cruzryan/OpenDOG/CAD/STL/b2/InterConnector.STL

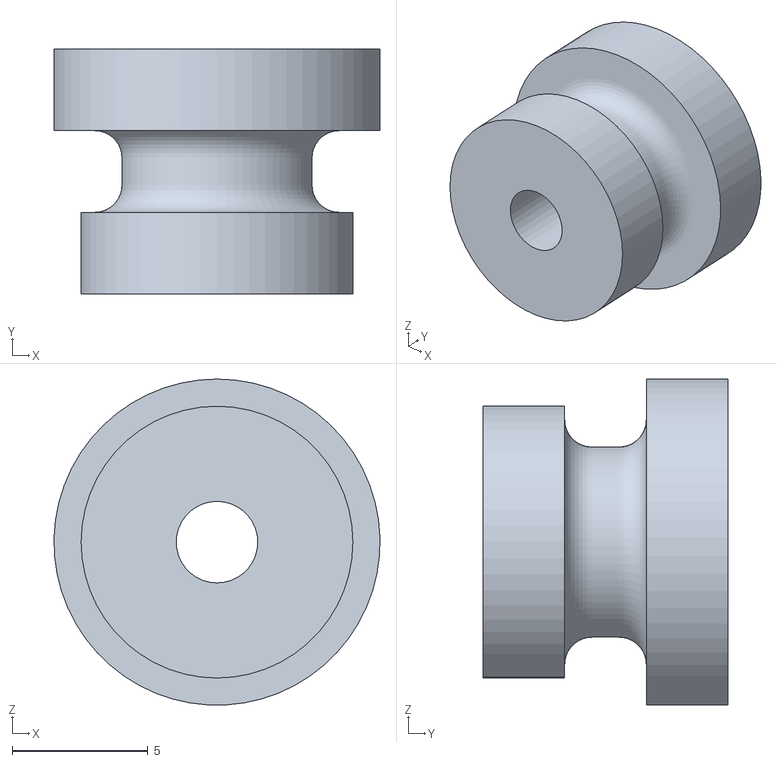
[picture p18: CAD file, 2025-06-15]
CAD/STL/b2/InterConnector.STL
12.0 x 9.00 x 12.0
