cruzryan/OpenDOG/CAD/STL/FINAL/A.STL

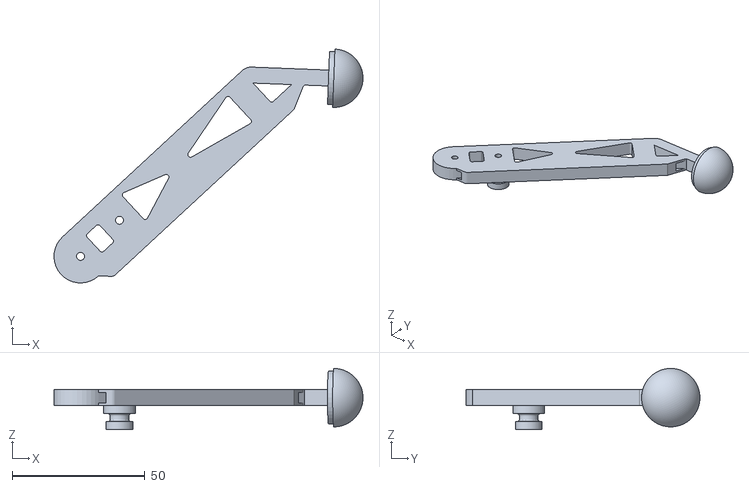
[picture p19: CAD file, 2025-06-15]
CAD/STL/FINAL/A.STL
116.4 x 88.0 x 23.0
