cruzryan/OpenDOG/CAD/STL/FULL/Chasis.STL

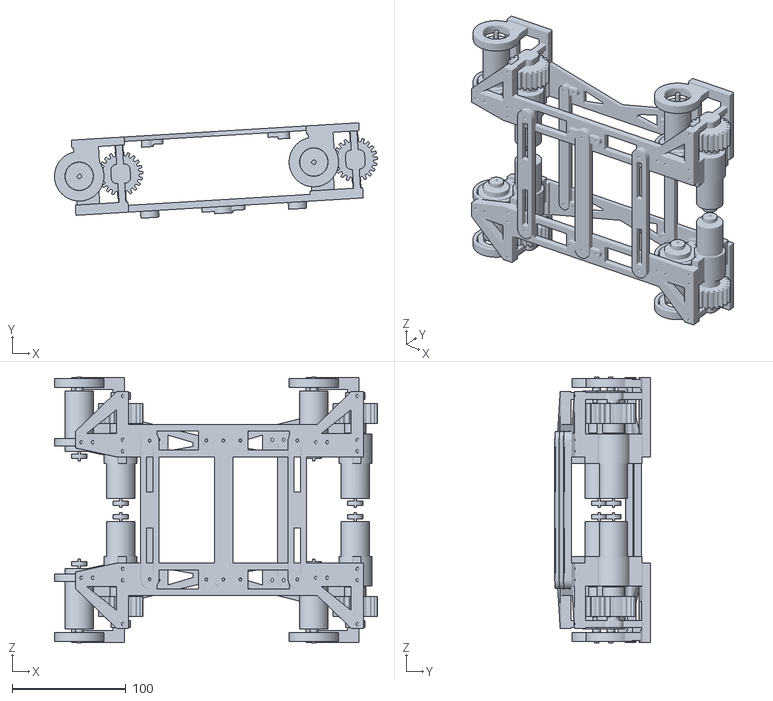
[picture p20: CAD file, 2025-06-15]
CAD/STL/FULL/Chasis.STL
283.8 x 83.9 x 233.7
