cruzryan/OpenDOG/CAD/STL/LEG/ShittyLeg - Cople-1.STL

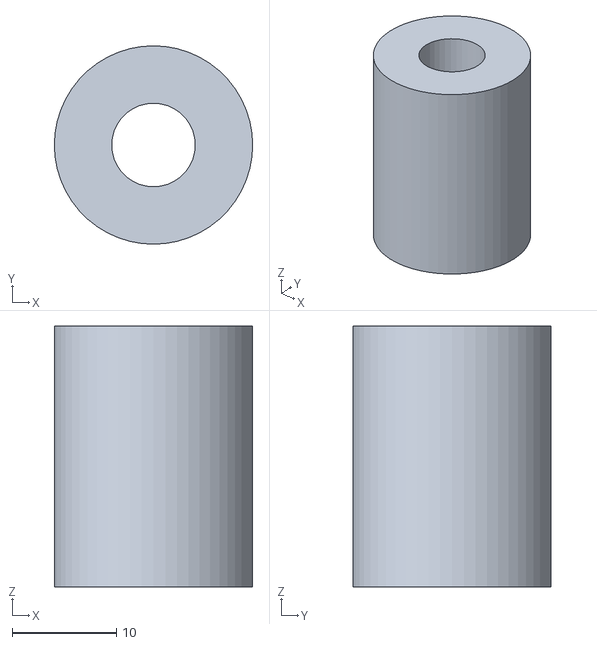
[picture p21: CAD file, 2025-06-15]
CAD/STL/LEG/ShittyLeg - Cople-1.STL
19.0 x 19.0 x 25.0
