cruzryan/OpenDOG/Code/mujoco/unitree_go1/assets/hip.stl

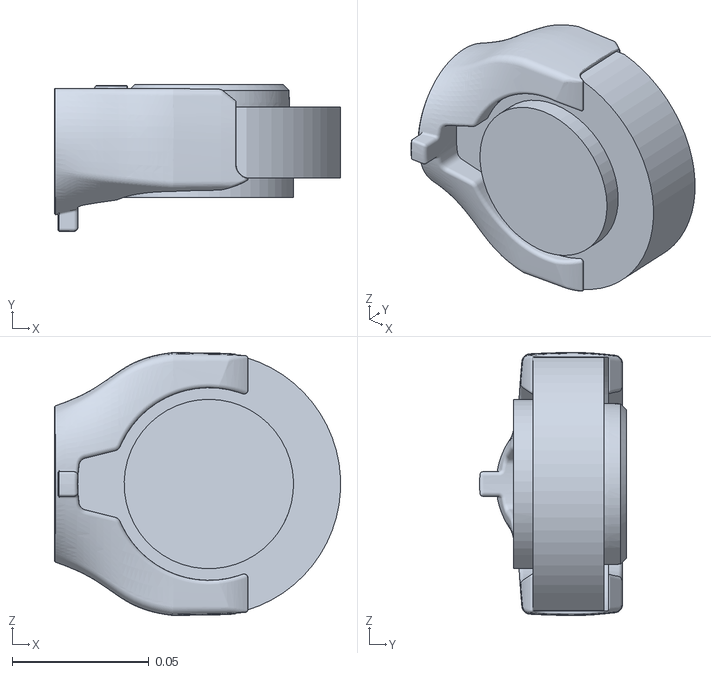
[picture p22: CAD file, 2025-03-04]
Code/mujoco/unitree_go1/assets/hip.stl
0.105 x 0.0538 x 0.0963
