cruzryan/OpenDOG/CAD/STL/b1/FeetLigament.STL

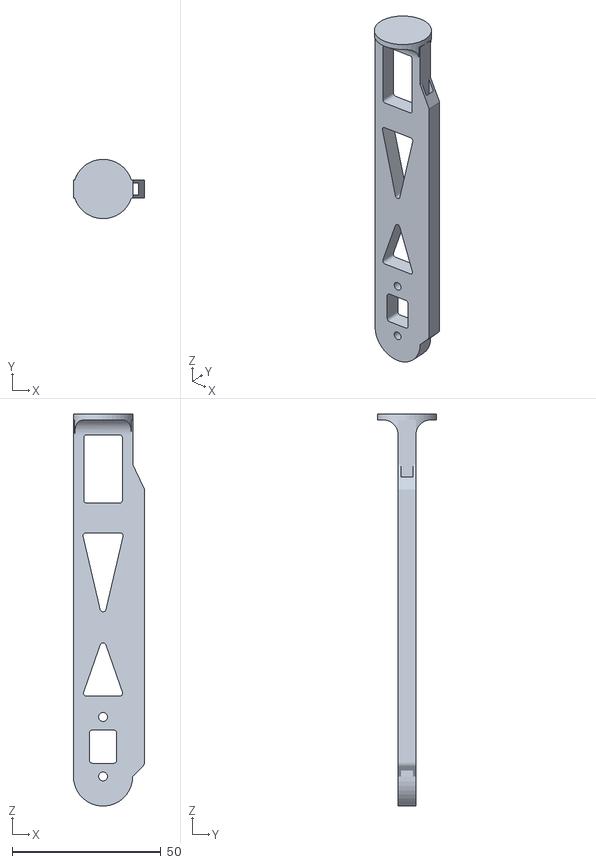
[picture p23: CAD file, 2025-06-15]
CAD/STL/b1/FeetLigament.STL
24.0 x 20.0 x 132.0
