cruzryan/OpenDOG/CAD/STL/b3/Balero6mmHolder.STL

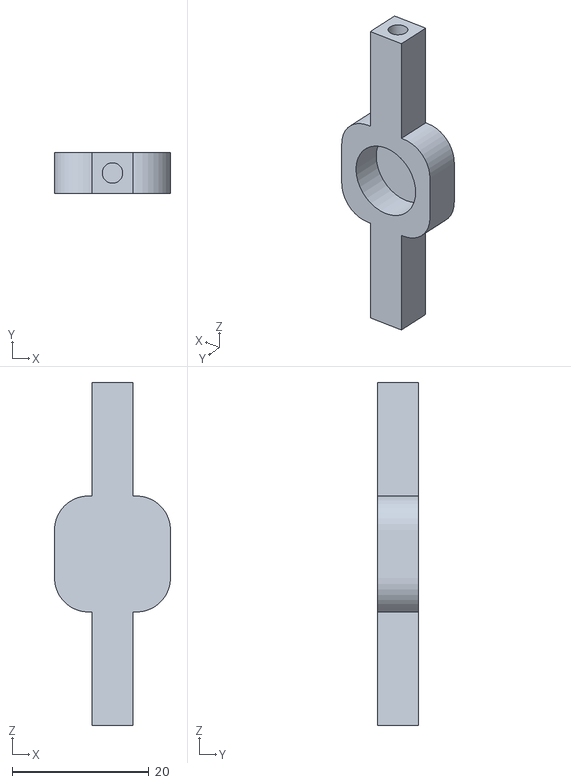
[picture p24: CAD file, 2025-06-15]
CAD/STL/b3/Balero6mmHolder.STL
17.0 x 6.00 x 50.2
