cruzryan/OpenDOG/CAD/STL/LEG/ShittyLeg - MotorCopler-1.STL

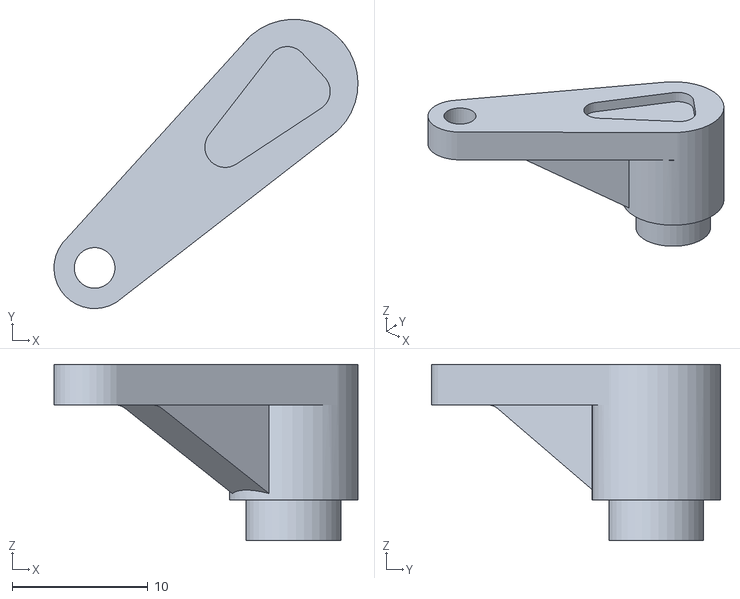
[picture p25: CAD file, 2025-06-15]
CAD/STL/LEG/ShittyLeg - MotorCopler-1.STL
22.4 x 21.3 x 13.0
