cruzryan/OpenDOG/CAD/STL/MUJOCO/ShittyLeg.STL

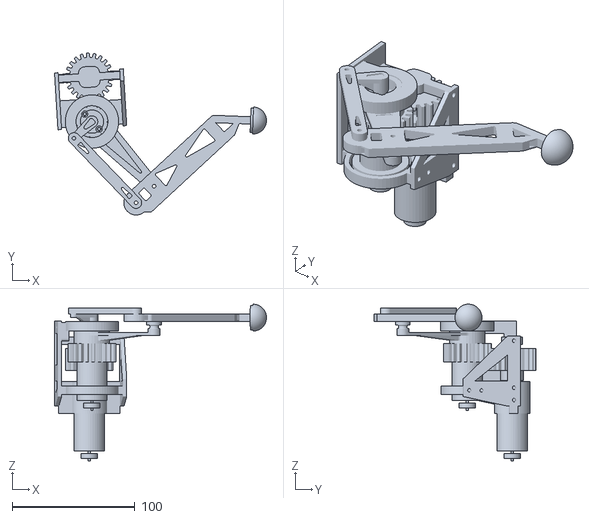
[picture p26: CAD file, 2025-06-15]
CAD/STL/MUJOCO/ShittyLeg.STL
172.9 x 132.1 x 127.8
