cruzryan/OpenDOG/CAD/STL/TopLegConnectorFIXEDLOL.STL

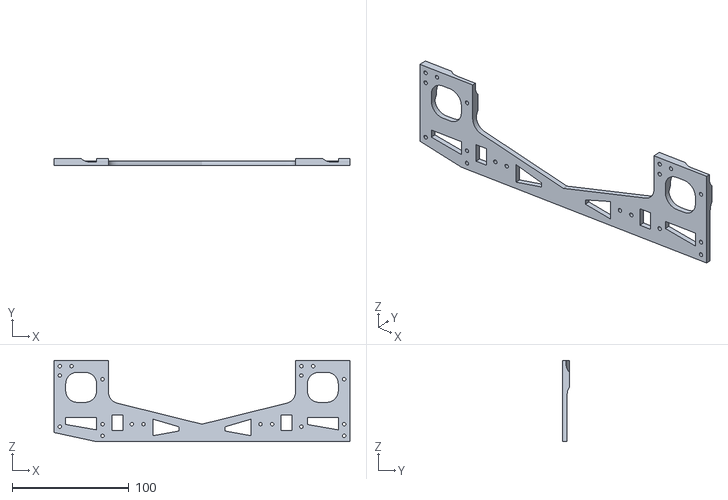
[picture p27: CAD file, 2025-06-15]
CAD/STL/TopLegConnectorFIXEDLOL.STL
253.0 x 6.00 x 69.6
