cruzryan/OpenDOG/Code/mujoco/our_robot/assets/left_calf.stl

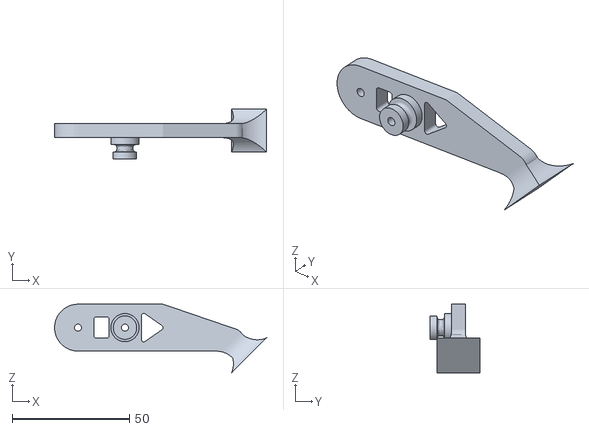
[picture p28: CAD file, 2025-05-04]
Code/mujoco/our_robot/assets/left_calf.stl
90.2 x 21.1 x 29.3
