cruzryan/OpenDOG/Code/mujoco/unitree_go1/assets/calf.stl

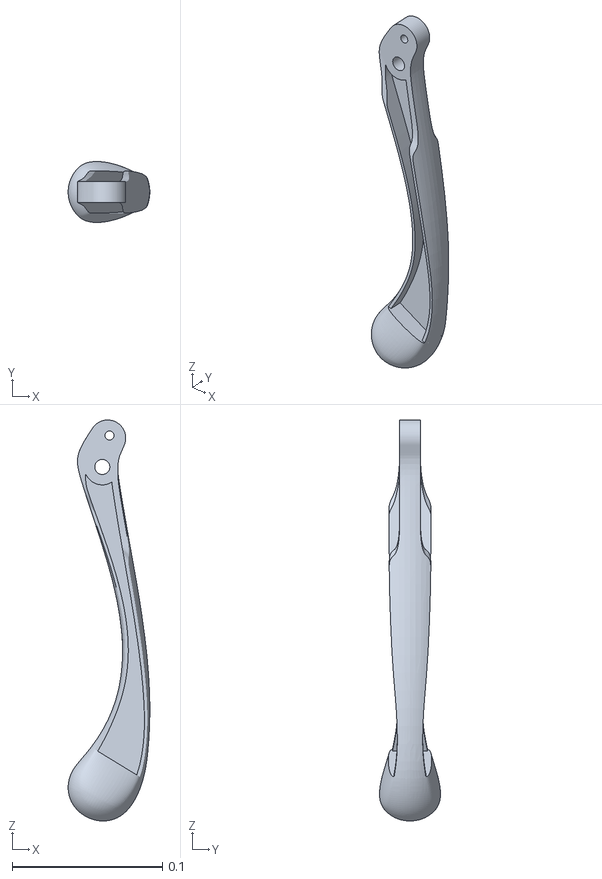
[picture p29: CAD file, 2025-03-04]
Code/mujoco/unitree_go1/assets/calf.stl
0.0543 x 0.0405 x 0.266
