cruzryan/OpenDOG/CAD/STL/b3/FeetLigament.STL

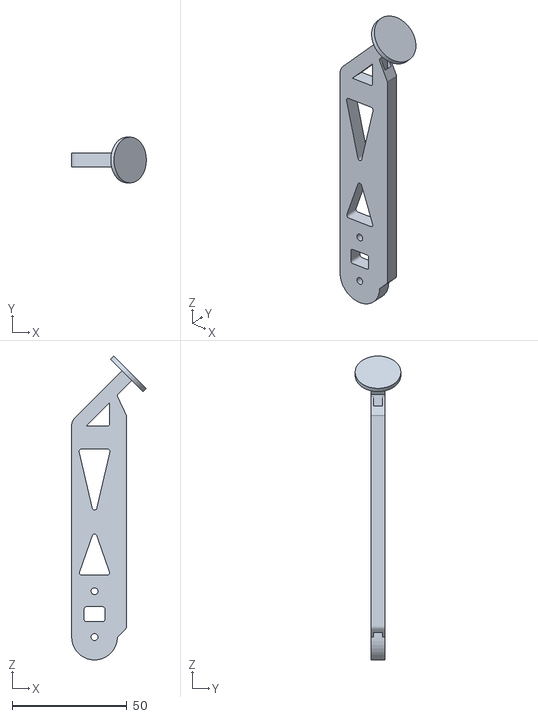
[picture p30: CAD file, 2025-06-15]
CAD/STL/b3/FeetLigament.STL
32.6 x 20.0 x 132.6
