cruzryan/OpenDOG/CAD/STL/TopLegConnector FILLED.STL

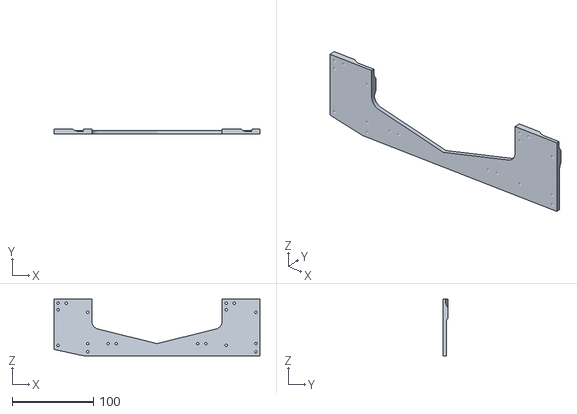
[picture p31: CAD file, 2025-06-15]
CAD/STL/TopLegConnector FILLED.STL
253.0 x 6.00 x 69.6
