cruzryan/OpenDOG/Code/mujoco/our_robot/assets/chasis.stl

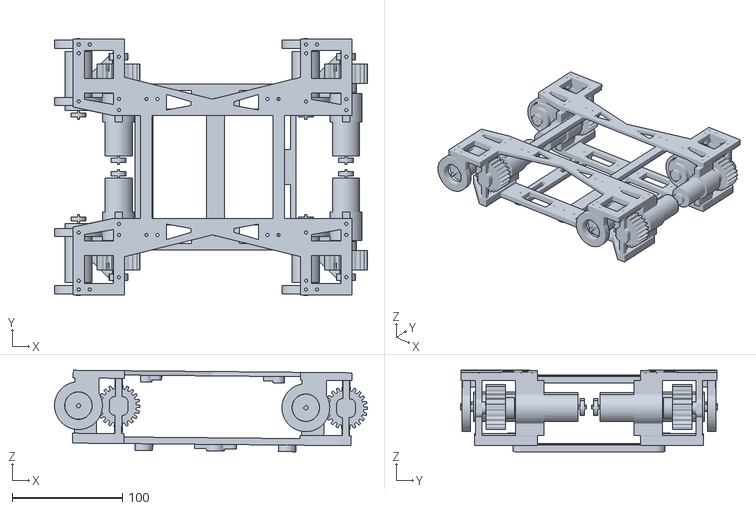
[picture p32: CAD file, 2025-05-04]
Code/mujoco/our_robot/assets/chasis.stl
284.3 x 233.7 x 74.1
