cruzryan/OpenDOG/Code/mujoco/unitree_go1/assets/thigh_mirror.stl

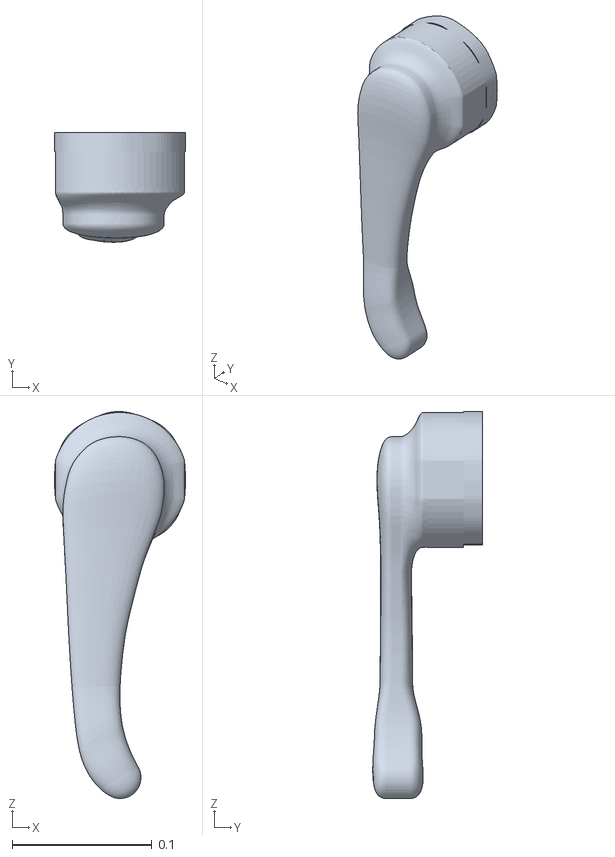
[picture p33: CAD file, 2025-03-04]
Code/mujoco/unitree_go1/assets/thigh_mirror.stl
0.094 x 0.0784 x 0.277
