cruzryan/OpenDOG/CAD/STL/b1/PartConnector.STL

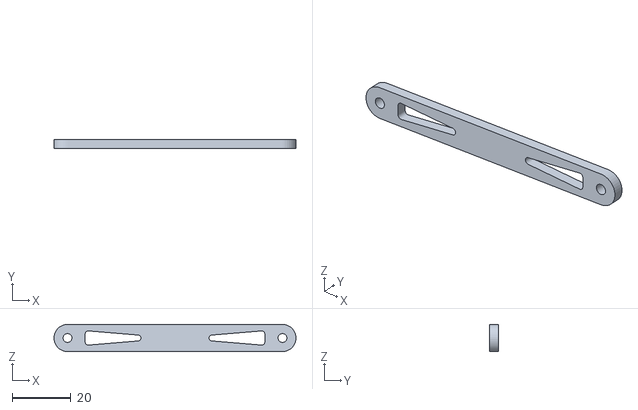
[picture p34: CAD file, 2025-06-15]
CAD/STL/b1/PartConnector.STL
82.2 x 3.00 x 9.22
