cruzryan/OpenDOG/CAD/STL/b3/TopConnectorLeg.STL

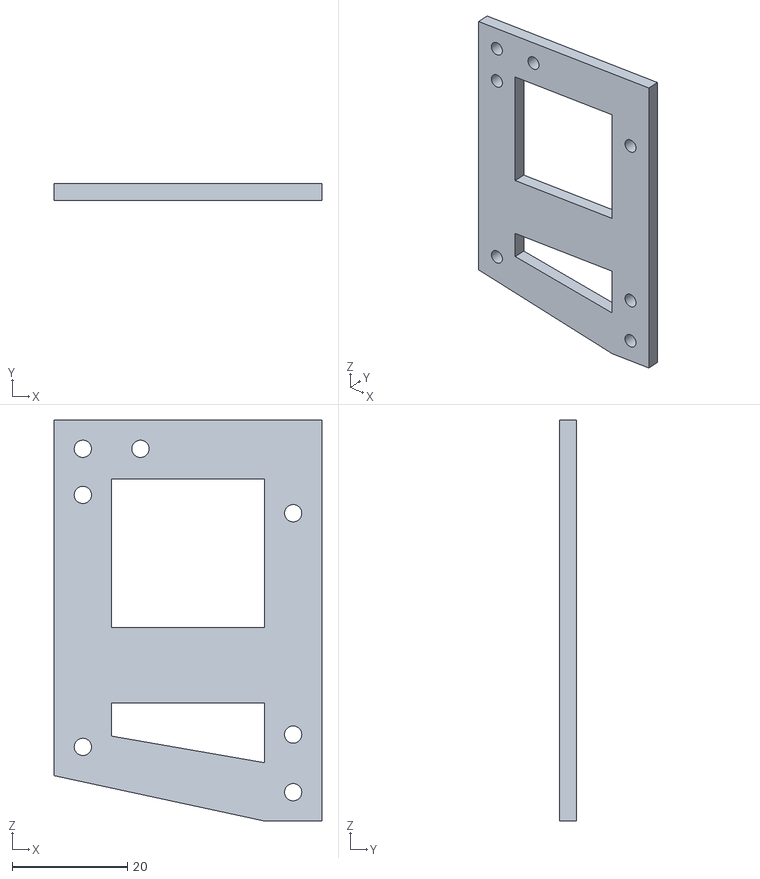
[picture p35: CAD file, 2025-06-15]
CAD/STL/b3/TopConnectorLeg.STL
46.5 x 3.00 x 69.6
