cruzryan/OpenDOG/CAD/STL/BALERO A.STL

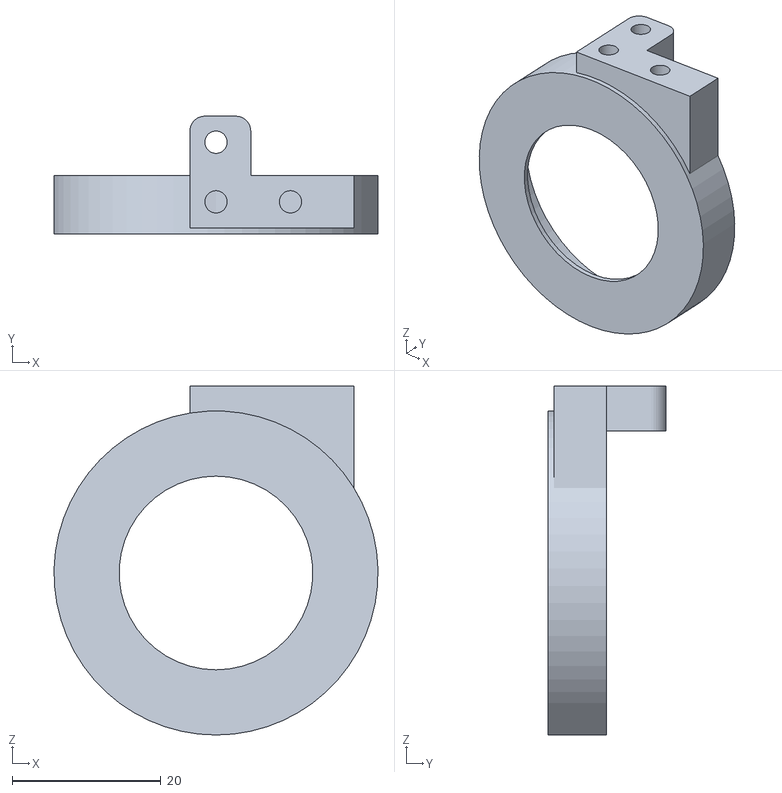
[picture p36: CAD file, 2025-06-15]
CAD/STL/BALERO A.STL
43.5 x 15.8 x 46.8
