cruzryan/OpenDOG/CAD/STL/FINAL/ENGRANE.STL

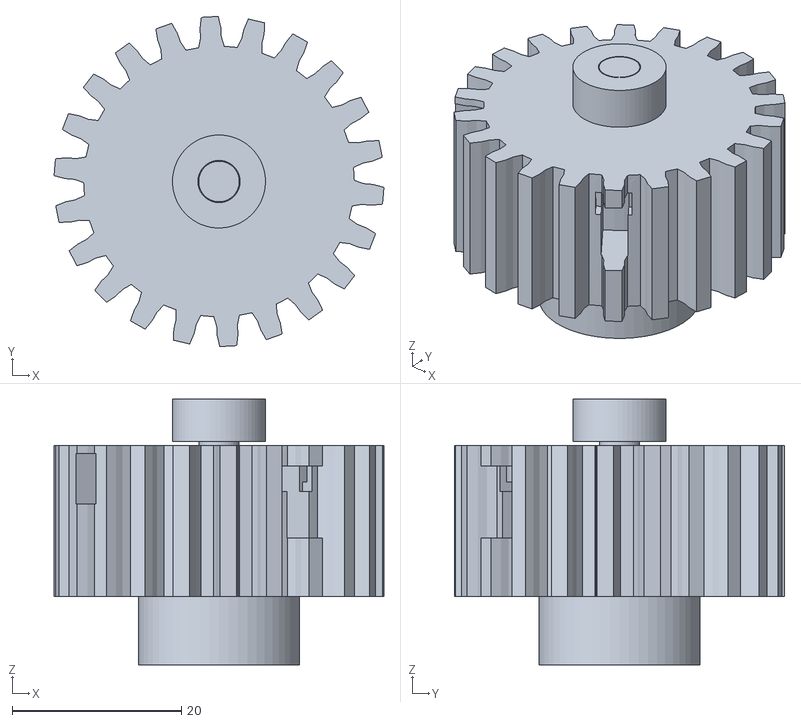
[picture p37: CAD file, 2025-06-15]
CAD/STL/FINAL/ENGRANE.STL
39.0 x 39.1 x 31.4
