cruzryan/OpenDOG/CAD/STL/LEG/ShittyLeg - PartConnector-1.STL

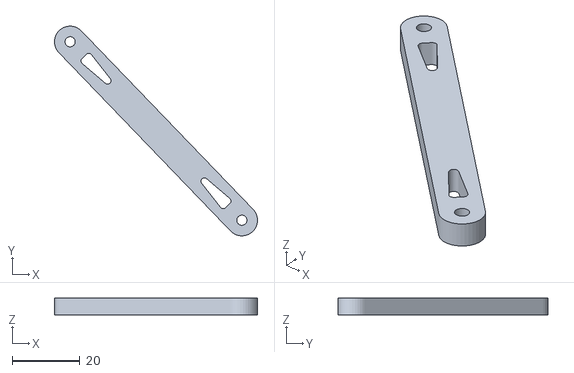
[picture p38: CAD file, 2025-06-15]
CAD/STL/LEG/ShittyLeg - PartConnector-1.STL
59.8 x 61.8 x 5.00
