cruzryan/OpenDOG/CAD/STL/MUJOCO/B.STL

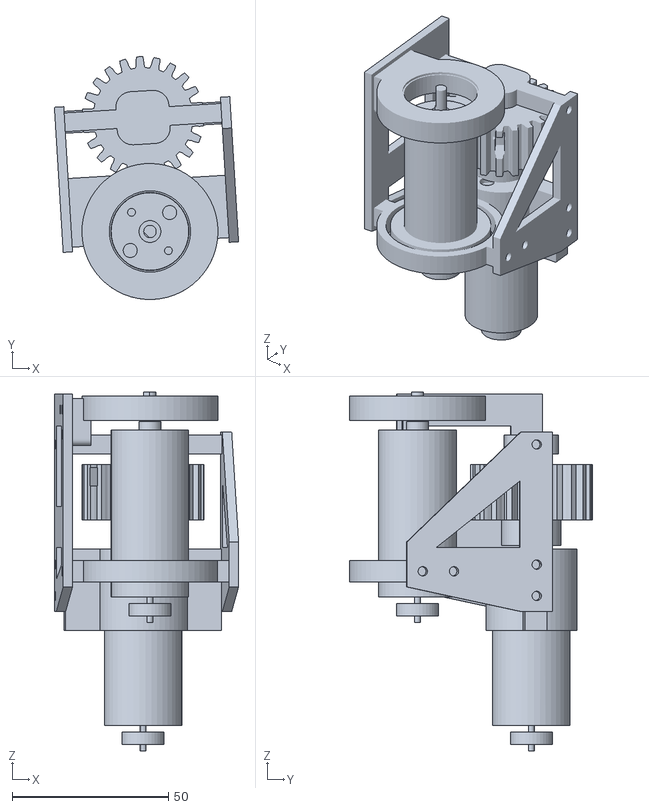
[picture p39: CAD file, 2025-06-15]
CAD/STL/MUJOCO/B.STL
58.9 x 77.7 x 114.8
