cruzryan/OpenDOG/CAD/STL/LEG/ShittyLeg - Balero-1.STL

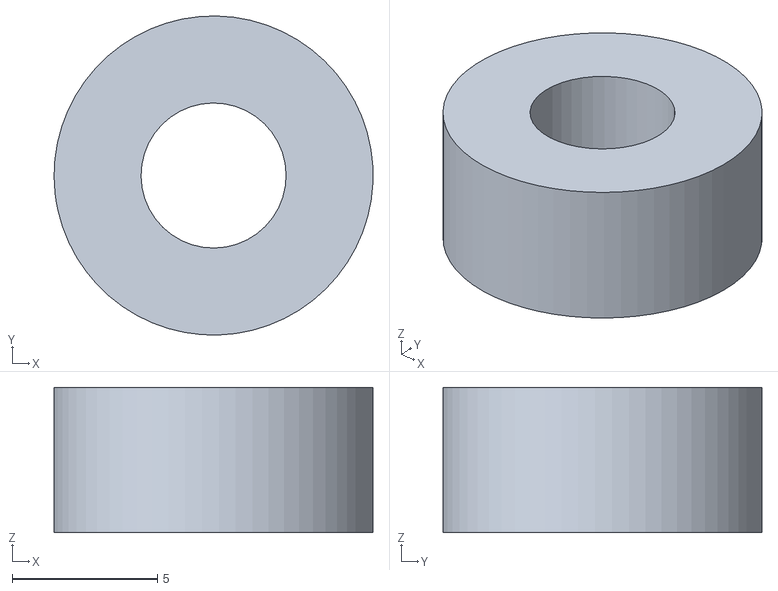
[picture p40: CAD file, 2025-06-15]
CAD/STL/LEG/ShittyLeg - Balero-1.STL
11.0 x 11.0 x 5.00
