cruzryan/OpenDOG/Code/mujoco/our_robot/assets/paw.stl

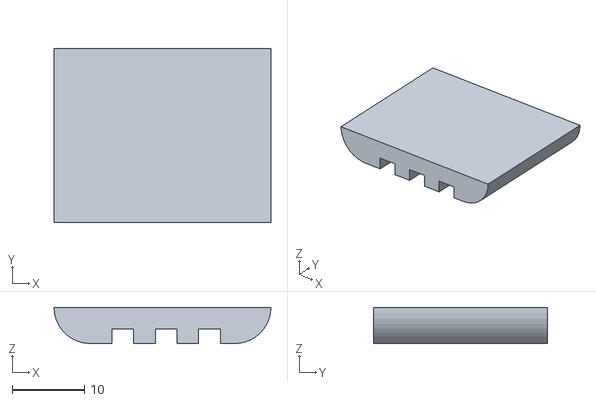
[picture p41: CAD file, 2025-05-04]
Code/mujoco/our_robot/assets/paw.stl
30.0 x 24.0 x 4.98
