cruzryan/OpenDOG/CAD/STL/ft.STL

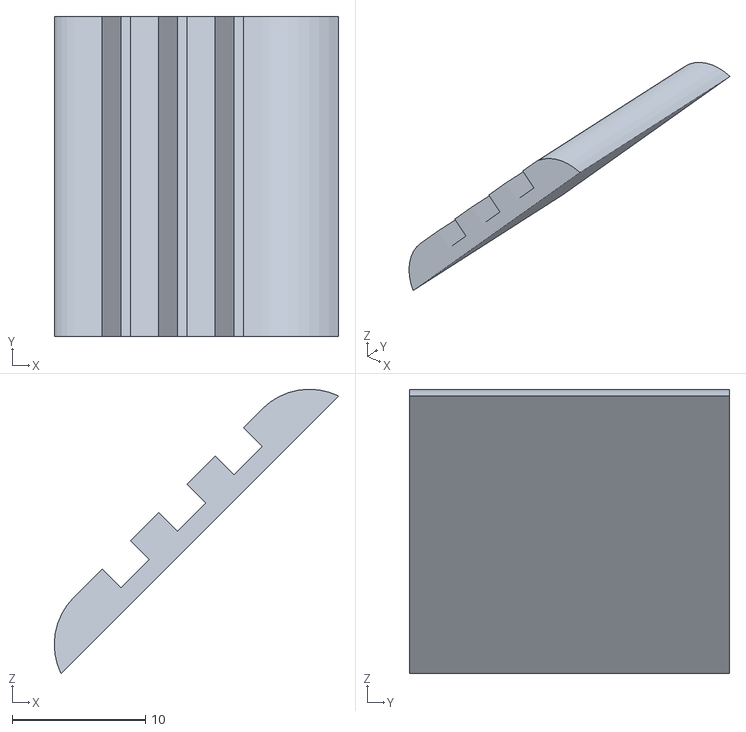
[picture p42: CAD file, 2025-06-15]
CAD/STL/ft.STL
21.3 x 24.0 x 21.3
