cruzryan/OpenDOG/CAD/STL/LEG/ShittyLeg - Motor GM25 V1-1.STL

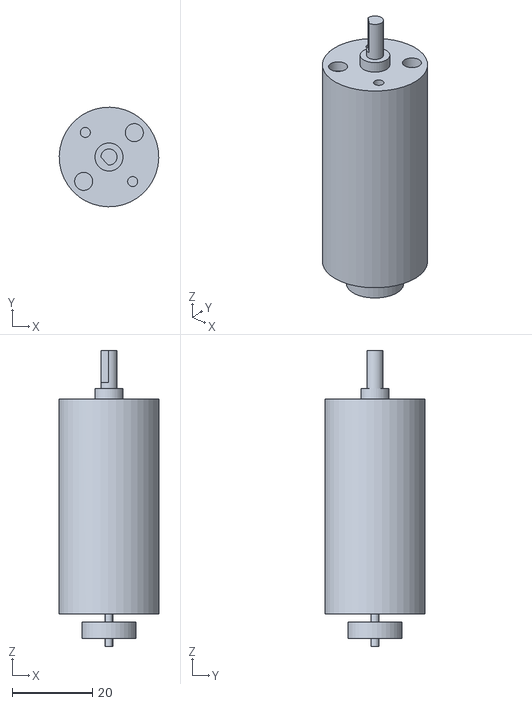
[picture p43: CAD file, 2025-06-15]
CAD/STL/LEG/ShittyLeg - Motor GM25 V1-1.STL
24.8 x 24.8 x 73.7
