cruzryan/OpenDOG/CAD/STL/b3/MotorCover2.STL

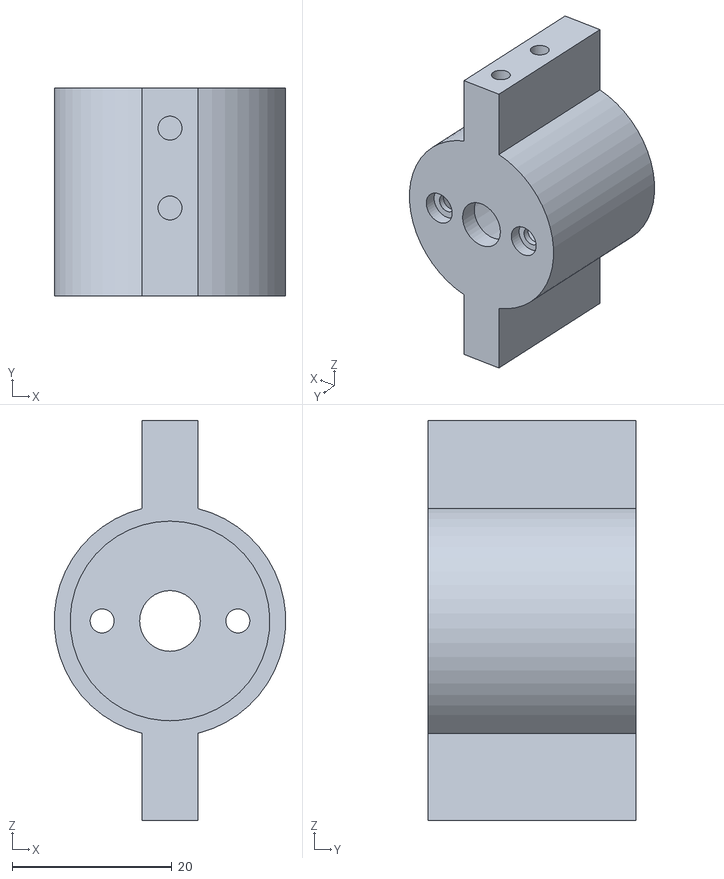
[picture p44: CAD file, 2025-06-15]
CAD/STL/b3/MotorCover2.STL
28.9 x 26.0 x 50.1
