cruzryan/OpenDOG/CAD/STL/CHASIS_NO_TRIG.stl

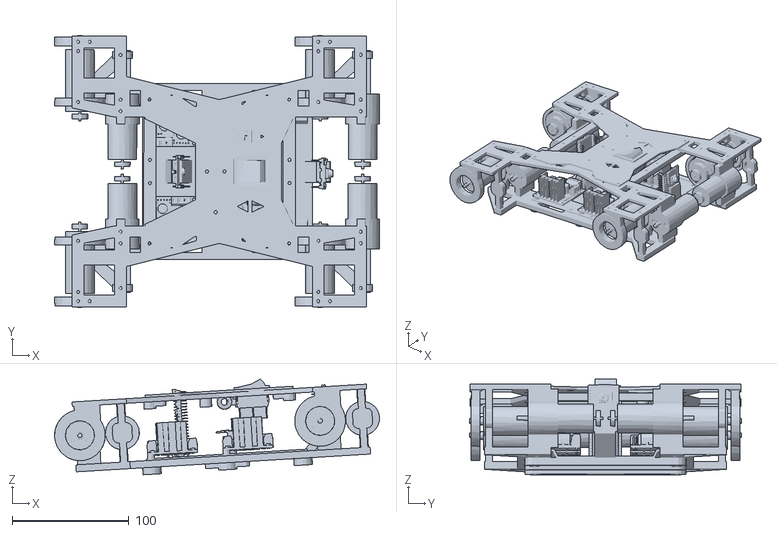
[picture p45: CAD file, 2025-06-15]
CAD/STL/CHASIS_NO_TRIG.stl
278.9 x 233.8 x 82.1
