cruzryan/OpenDOG/CAD/STL/LEG/ShittyLeg - Balero25mmv5-1.STL

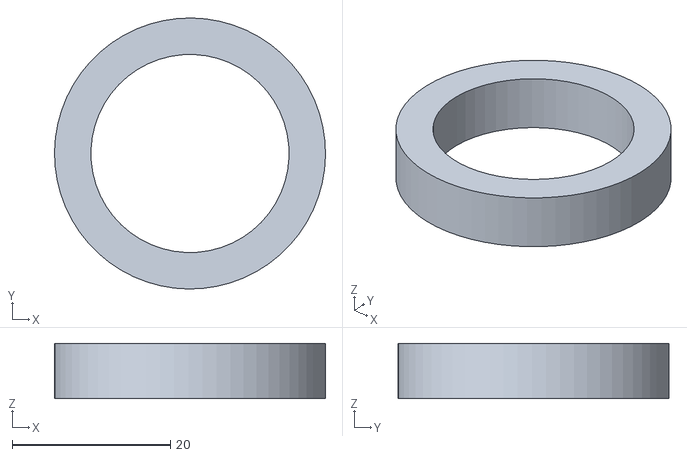
[picture p46: CAD file, 2025-06-15]
CAD/STL/LEG/ShittyLeg - Balero25mmv5-1.STL
34.2 x 34.2 x 7.00
