cruzryan/OpenDOG/CAD/STL/b3/BottomConnectorLeg3.STL

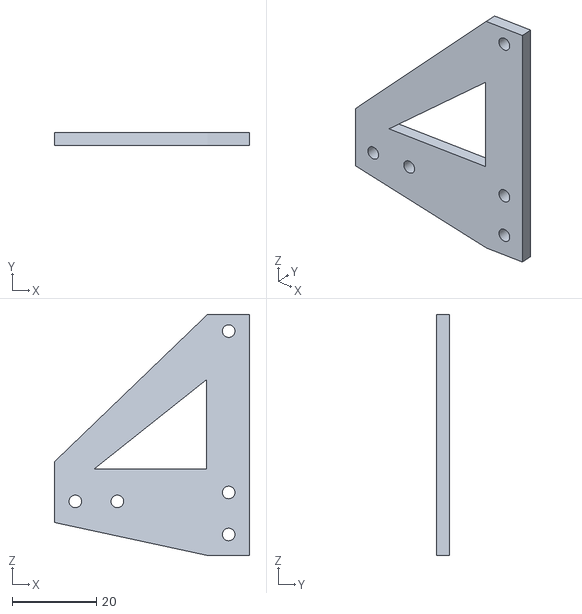
[picture p47: CAD file, 2025-06-15]
CAD/STL/b3/BottomConnectorLeg3.STL
46.5 x 3.00 x 57.4
