cruzryan/OpenDOG/CAD/STL/LEG/ShittyLeg - BaleroHolder-1.STL

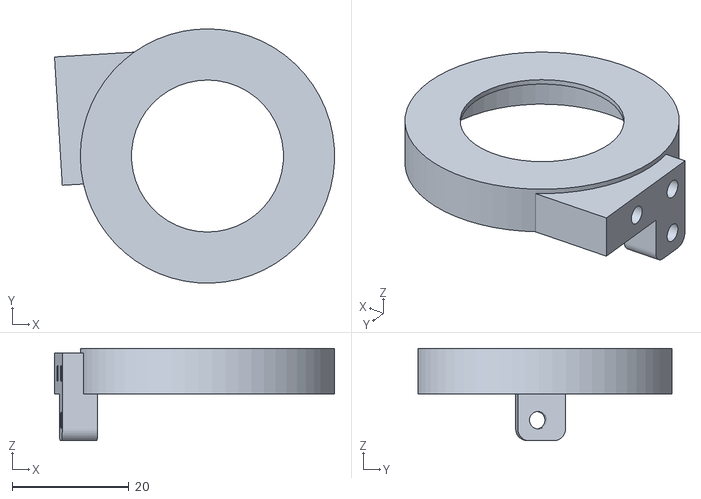
[picture p48: CAD file, 2025-06-15]
CAD/STL/LEG/ShittyLeg - BaleroHolder-1.STL
47.9 x 43.5 x 15.8
