cruzryan/OpenDOG/CAD/STL/LEG/ShittyLeg - FeetLigament-1.STL

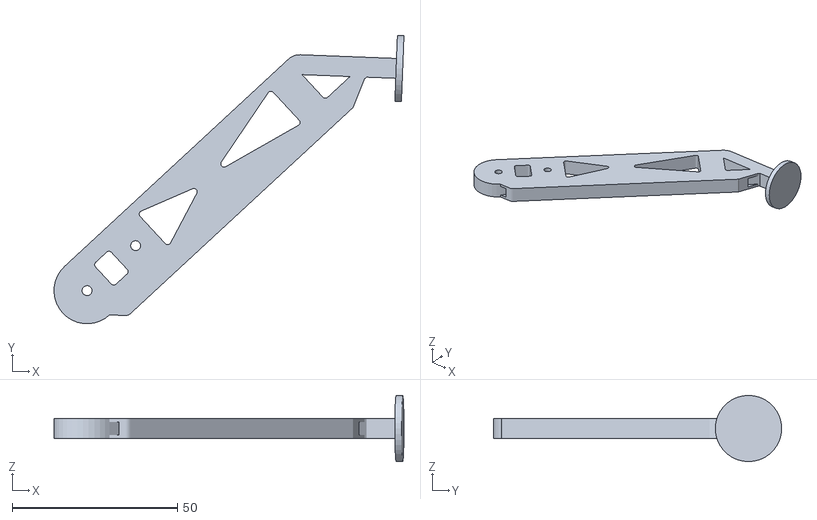
[picture p49: CAD file, 2025-06-15]
CAD/STL/LEG/ShittyLeg - FeetLigament-1.STL
105.7 x 87.1 x 20.0
