cruzryan/OpenDOG/CAD/STL/tstfeet.STL

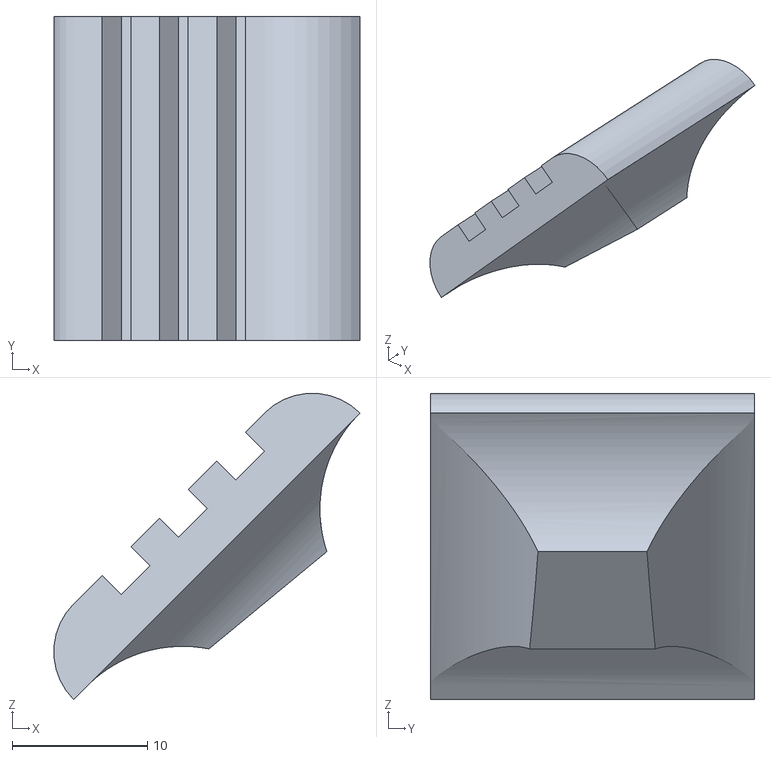
[picture p50: CAD file, 2025-06-15]
CAD/STL/tstfeet.STL
22.7 x 24.0 x 22.7
