cruzryan/OpenDOG/CAD/STL/Feet1.STL

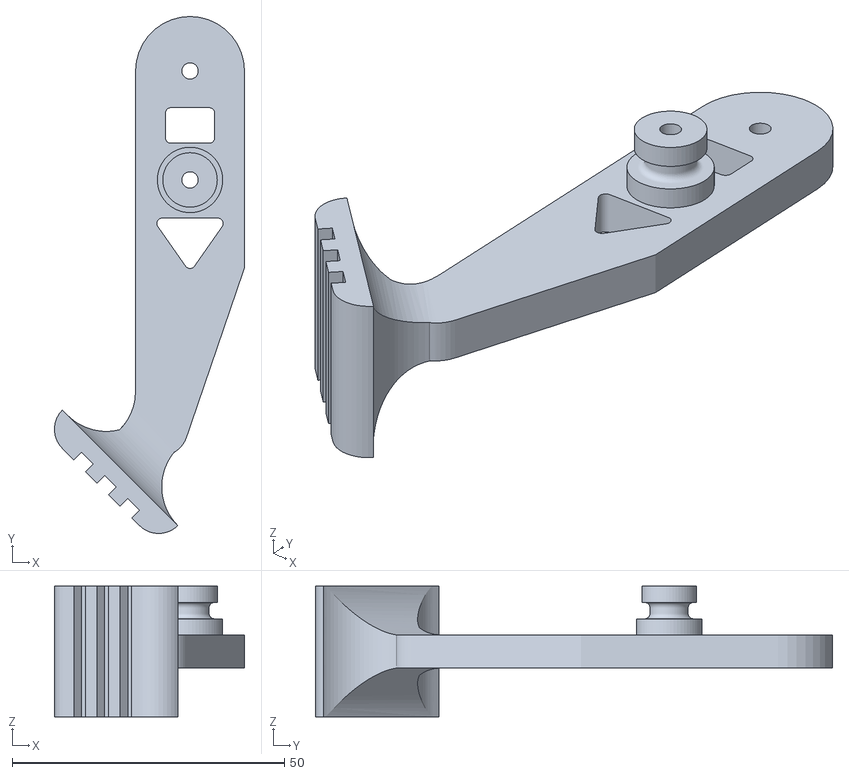
[picture p51: CAD file, 2025-06-15]
CAD/STL/Feet1.STL
34.9 x 94.9 x 24.0
