cruzryan/OpenDOG/CAD/STL/LEG/ShittyLeg - BottomConnectorLeg3-1.STL

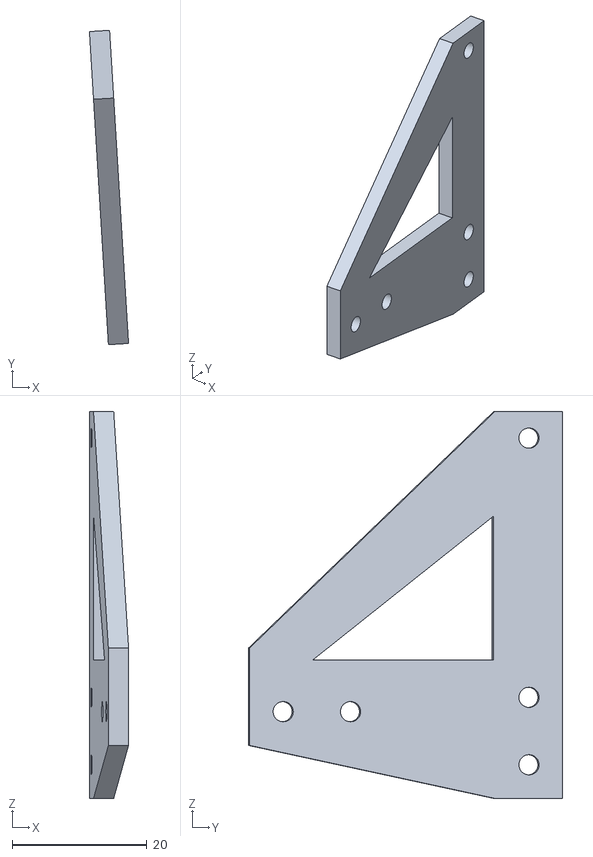
[picture p52: CAD file, 2025-06-15]
CAD/STL/LEG/ShittyLeg - BottomConnectorLeg3-1.STL
5.81 x 46.6 x 57.4
