cruzryan/OpenDOG/CAD/STL/LEG/ShittyLeg - Foot-1.STL

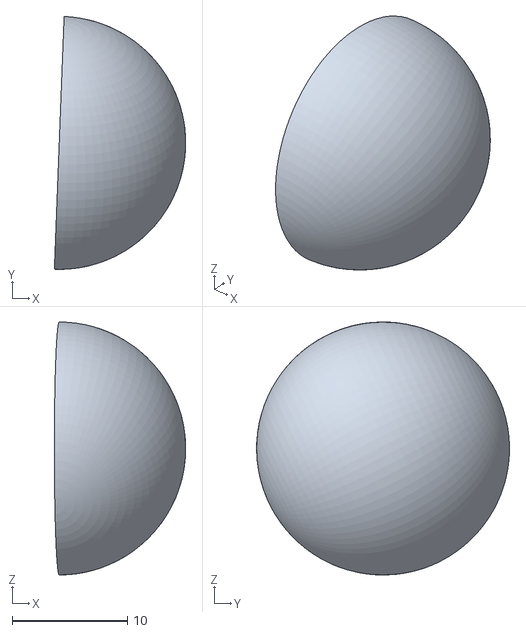
[picture p53: CAD file, 2025-06-15]
CAD/STL/LEG/ShittyLeg - Foot-1.STL
11.4 x 22.0 x 22.0
