cruzryan/OpenDOG/CAD/STL/NEWBottomLegConnector.STL

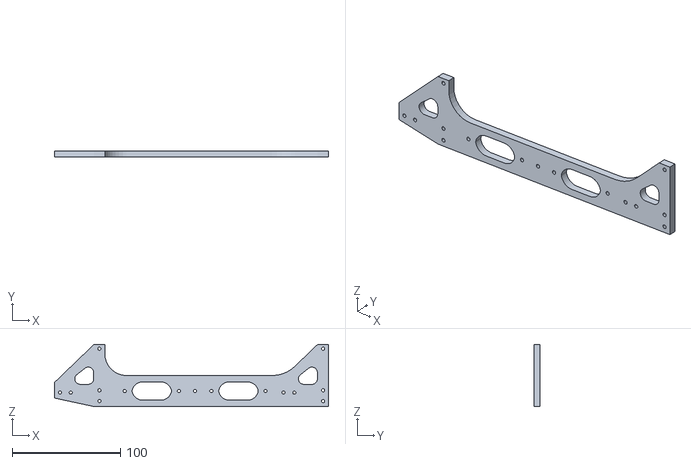
[picture p54: CAD file, 2025-06-15]
CAD/STL/NEWBottomLegConnector.STL
253.0 x 6.00 x 57.4
