cruzryan/OpenDOG/CAD/STL/footy.SLDPRT

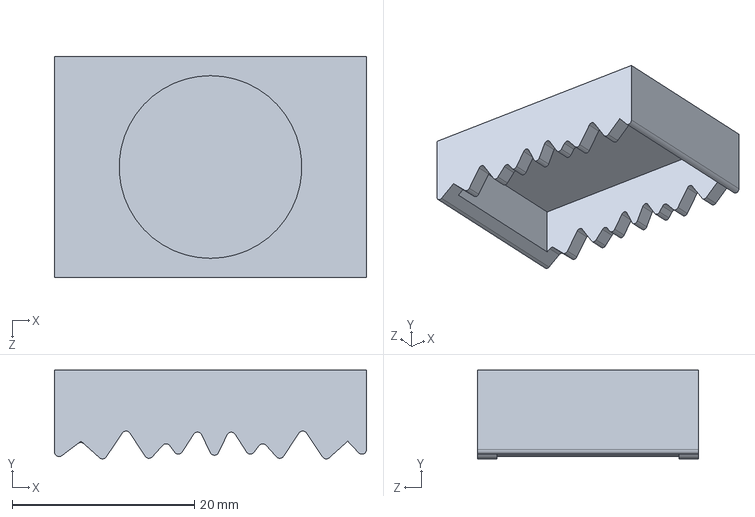
[picture p55: CAD file, 2025-06-15]
CAD/STL/footy.SLDPRT
34.2 x 9.74 x 24.2 mm
