cruzryan/OpenDOG/CAD/STL/BaleroHolder AAAA.SLDPRT

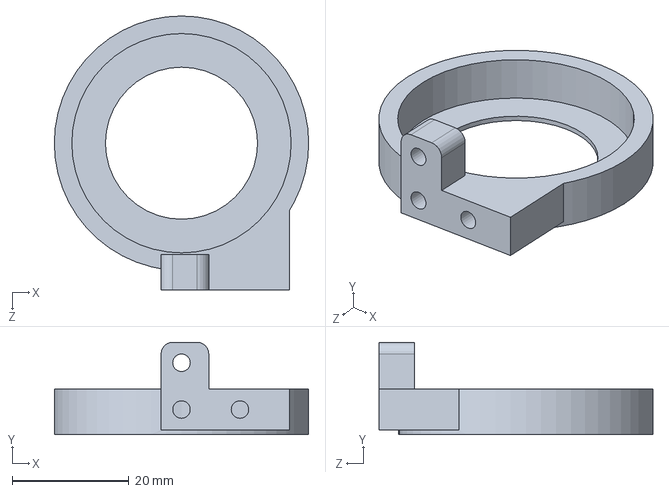
[picture p57: CAD file, 2025-06-15]
CAD/STL/BaleroHolder AAAA.SLDPRT
43.5 x 15.8 x 46.8 mm
