cruzryan/OpenDOG/CAD/STL/LEG/ShittyLeg - MotorCoverV5-1.STL

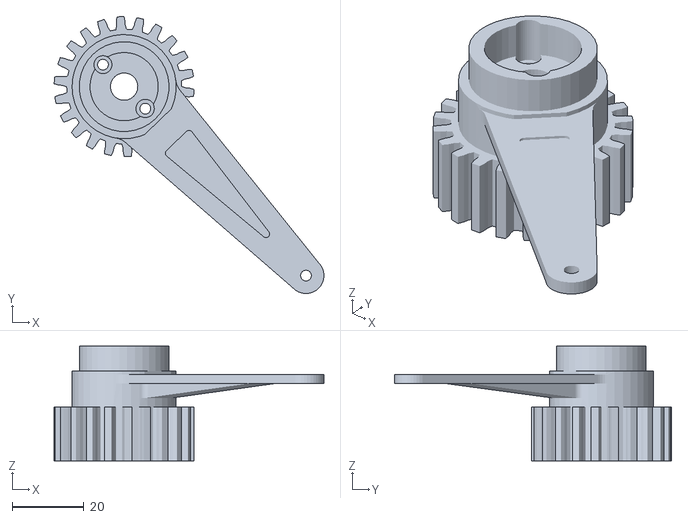
[picture p58: CAD file, 2025-06-15]
CAD/STL/LEG/ShittyLeg - MotorCoverV5-1.STL
75.1 x 77.1 x 32.0
