cruzryan/OpenDOG/CAD/STL/PartConnector50cmmmmmmmm.STL

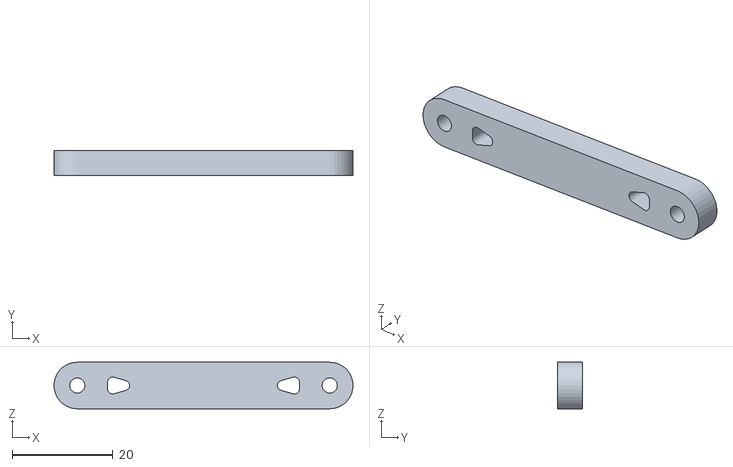
[picture p59: CAD file, 2025-06-15]
CAD/STL/PartConnector50cmmmmmmmm.STL
59.2 x 5.00 x 9.22
