cruzryan/OpenDOG/CAD/FeetLigament.SLDPRT

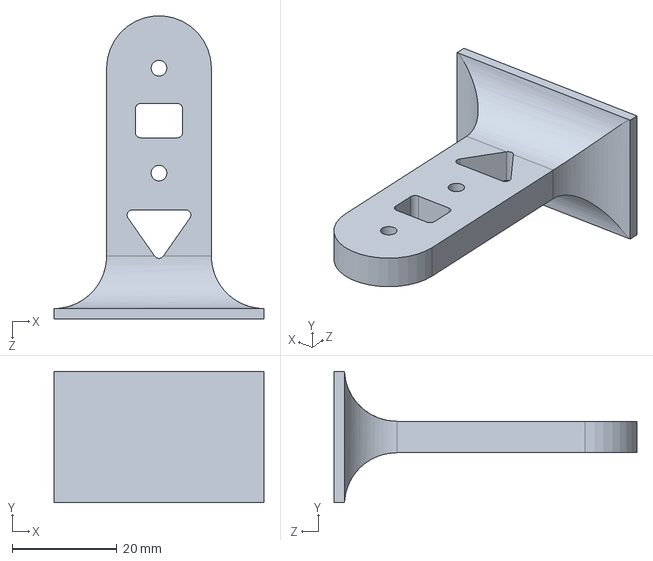
[picture p60: CAD file, 2025-06-15]
CAD/FeetLigament.SLDPRT
40.0 x 25.0 x 57.8 mm
