cruzryan/OpenDOG/CAD/STL/TopLegConnector2.2.STL

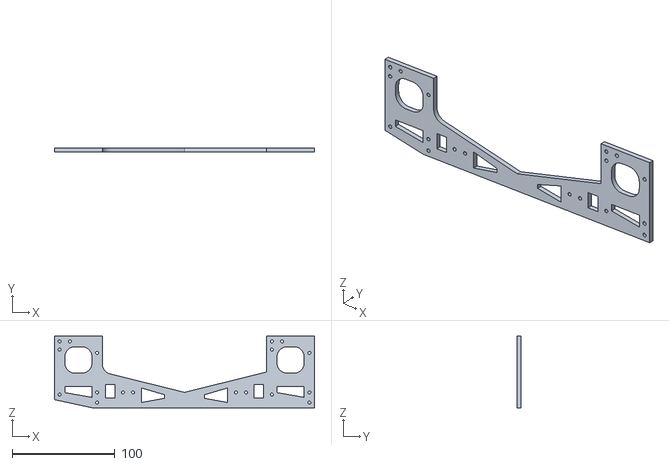
[picture p61: CAD file, 2025-06-15]
CAD/STL/TopLegConnector2.2.STL
253.0 x 4.00 x 69.6
