cruzryan/OpenDOG/CAD/STL/Floor2.STL

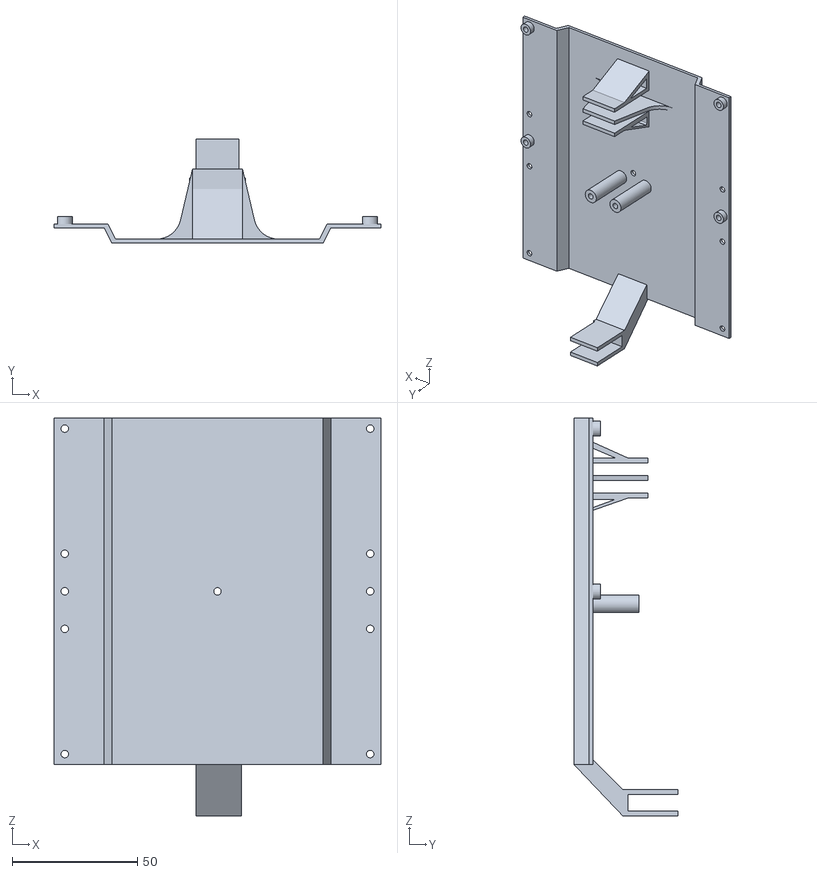
[picture p62: CAD file, 2025-06-15]
CAD/STL/Floor2.STL
130.5 x 41.5 x 159.0
