cruzryan/OpenDOG/CAD/STL/LEG/ShittyLeg - BaleroHolderTwo-1.STL

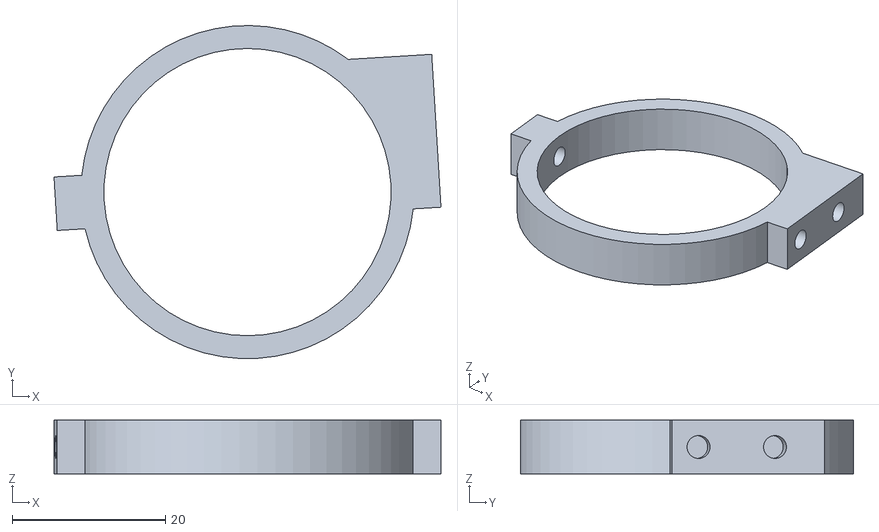
[picture p63: CAD file, 2025-06-15]
CAD/STL/LEG/ShittyLeg - BaleroHolderTwo-1.STL
50.5 x 43.5 x 7.00
