cruzryan/OpenDOG/CAD/STL/InterConnector1CMBIG.STL

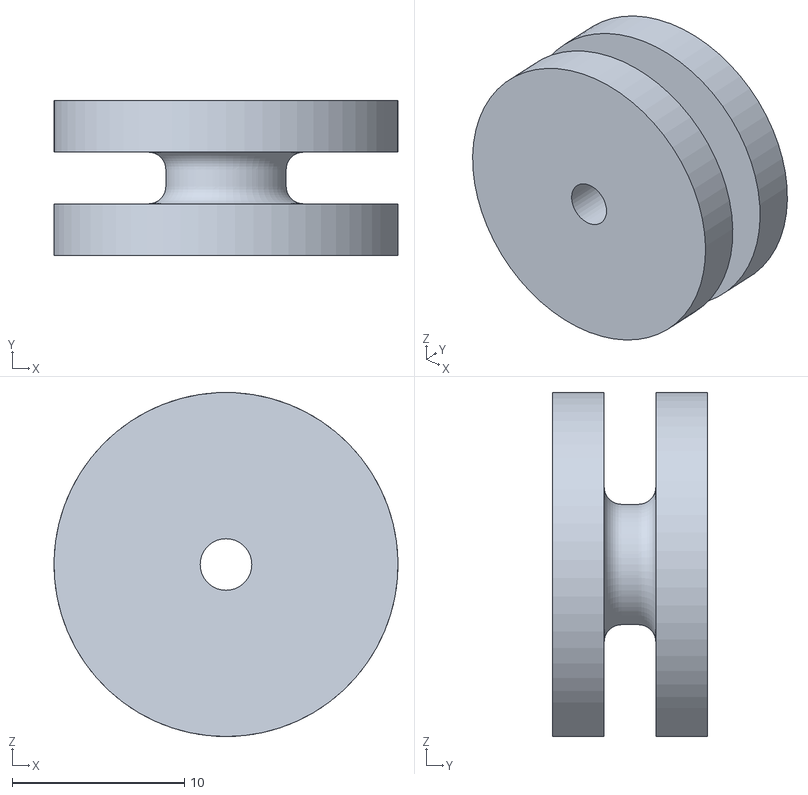
[picture p64: CAD file, 2025-06-15]
CAD/STL/InterConnector1CMBIG.STL
20.0 x 9.00 x 20.0
