cruzryan/OpenDOG/CAD/l515 holder v2.SLDPRT

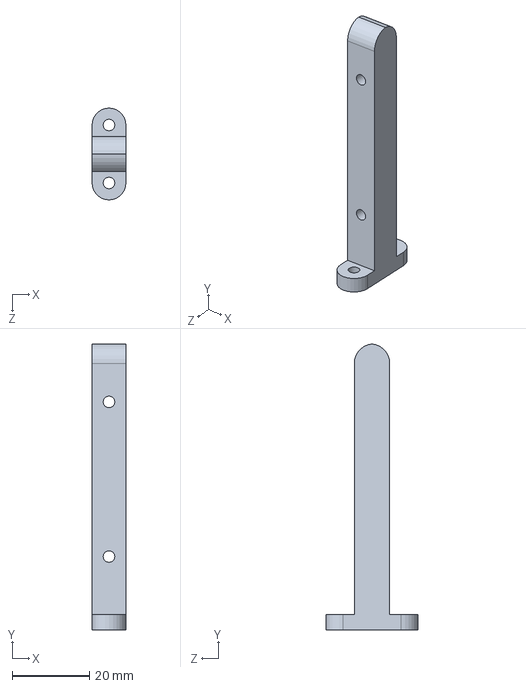
[picture p65: CAD file, 2025-06-15]
CAD/l515 holder v2.SLDPRT
8.74 x 74.0 x 23.7 mm
