cruzryan/OpenDOG/CAD/STL/Realshit.STL

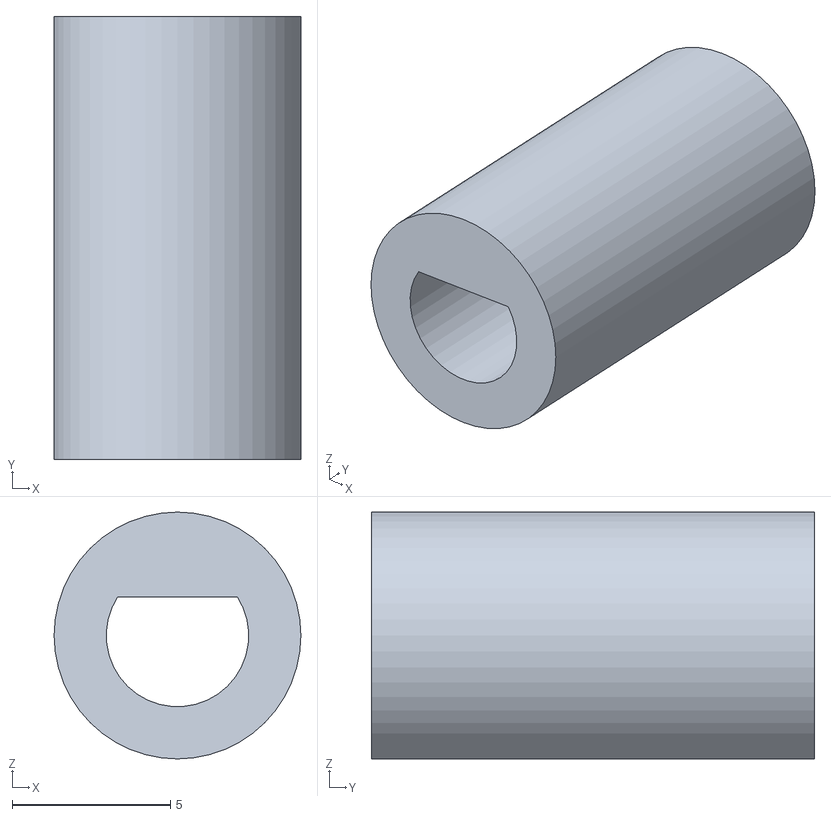
[picture p66: CAD file, 2025-06-15]
CAD/STL/Realshit.STL
7.80 x 14.0 x 7.80
