cruzryan/OpenDOG/CAD/TopLegConnectorOTHASIDE.SLDPRT

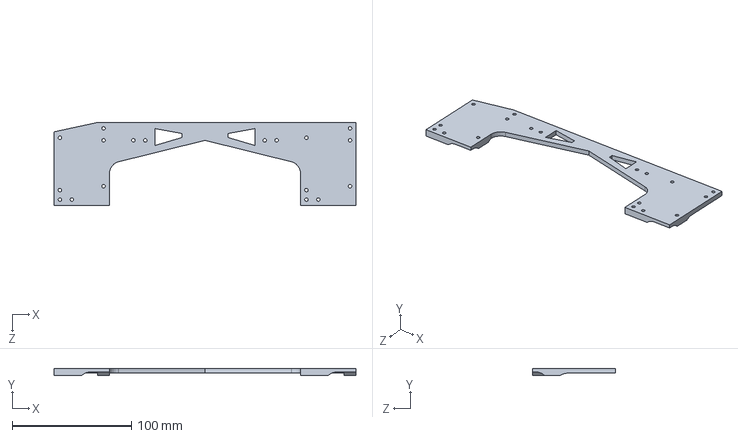
[picture p67: CAD file, 2025-06-15]
CAD/TopLegConnectorOTHASIDE.SLDPRT
253.0 x 6.00 x 69.6 mm
