cruzryan/OpenDOG/CAD/FeetLigamentSMOL45DEGREE.SLDPRT

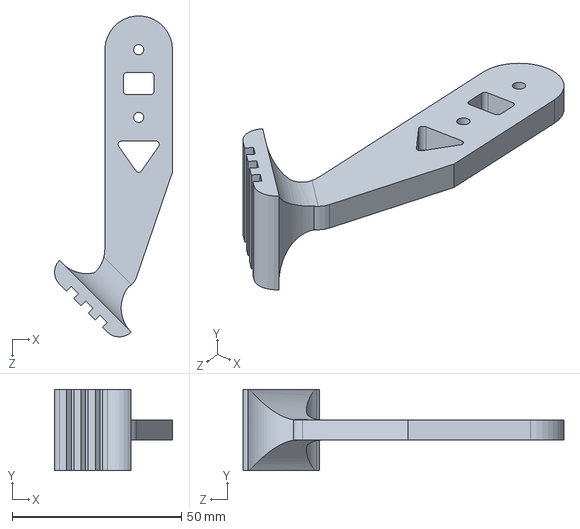
[picture p68: CAD file, 2025-06-15]
CAD/FeetLigamentSMOL45DEGREE.SLDPRT
34.9 x 24.0 x 94.9 mm
