cruzryan/OpenDOG/CAD/Tapa.SLDPRT

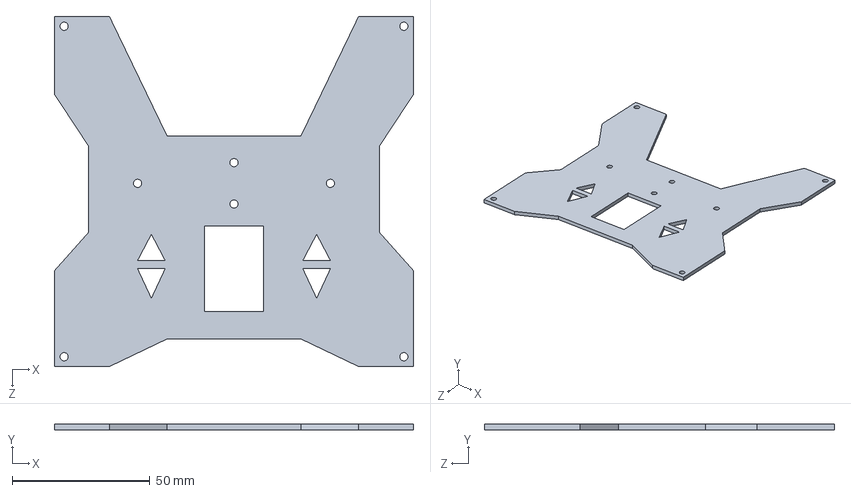
[picture p69: CAD file, 2025-06-15]
CAD/Tapa.SLDPRT
130.4 x 2.00 x 127.1 mm
