cruzryan/OpenDOG/CAD/Escudo-poli.SLDPRT

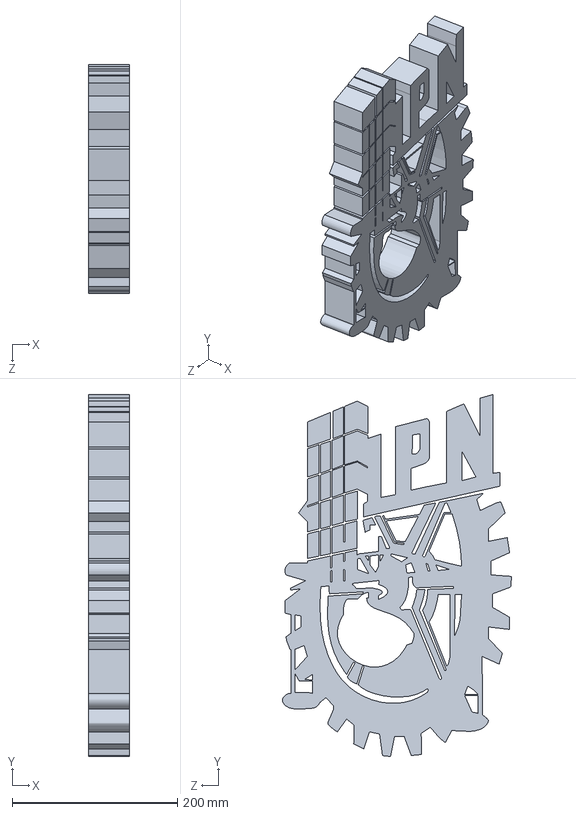
[picture p70: CAD file, 2025-06-15]
CAD/Escudo-poli.SLDPRT
50.0 x 438.2 x 277.4 mm
