cruzryan/OpenDOG/CAD/MotorCover2.SLDPRT

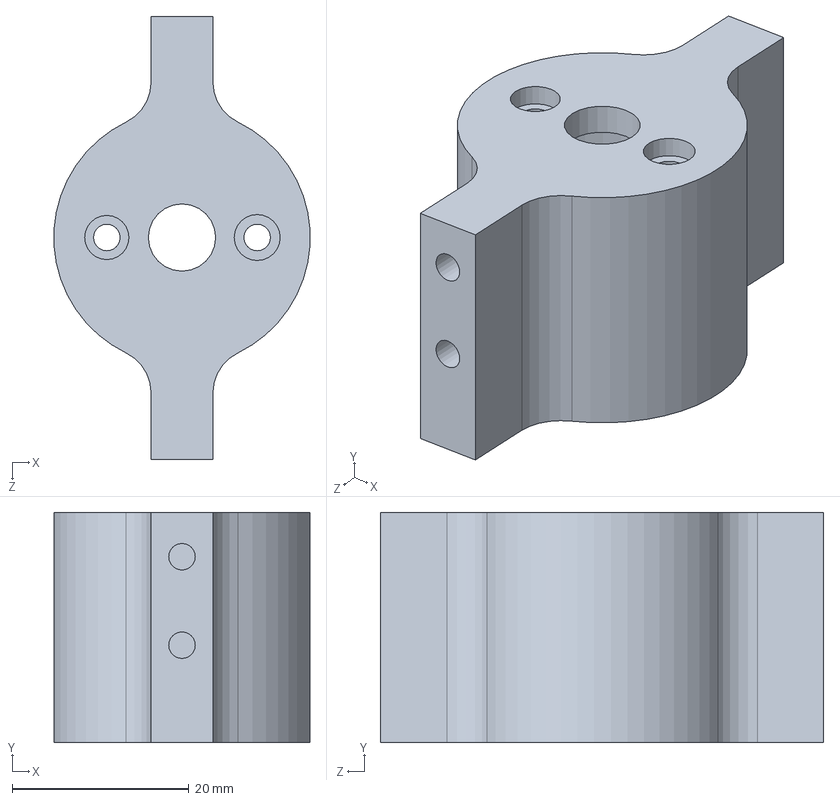
[picture p71: CAD file, 2025-06-15]
CAD/MotorCover2.SLDPRT
28.9 x 26.0 x 50.1 mm
