cruzryan/OpenDOG/CAD/cong tac 6 chan.STEP

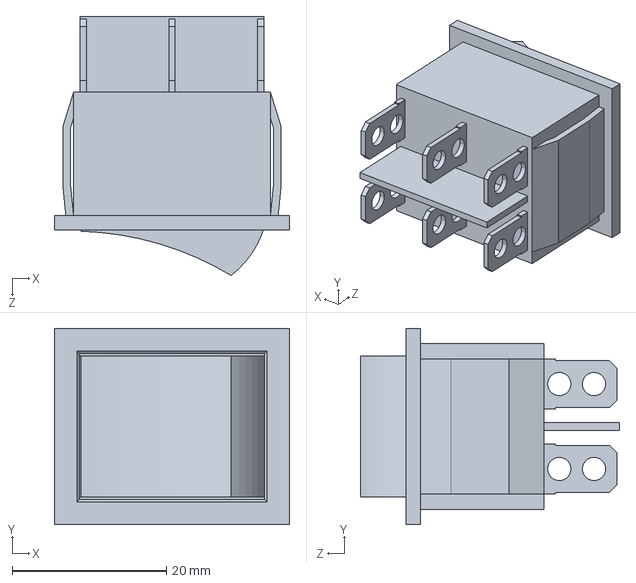
[picture p72: CAD file, 2025-02-11]
CAD/cong tac 6 chan.STEP
30.5 x 25.4 x 33.5 mm
