cruzryan/OpenDOG/CAD/BonesTop.SLDPRT

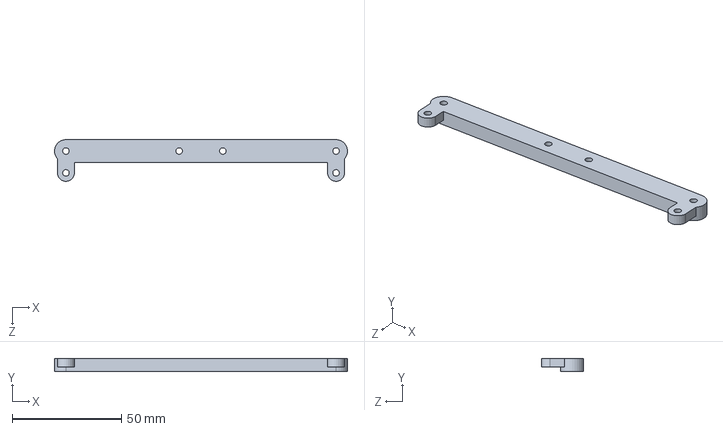
[picture p73: CAD file, 2025-02-11]
CAD/BonesTop.SLDPRT
133.8 x 6.00 x 19.1 mm
