cruzryan/OpenDOG/CAD/BonesMiddleBottom.SLDPRT

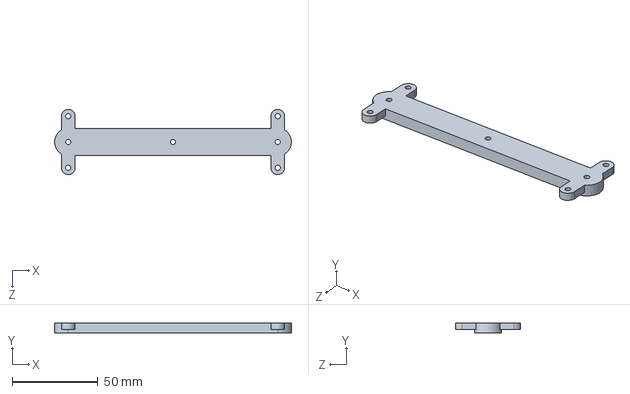
[picture p74: CAD file, 2025-02-11]
CAD/BonesMiddleBottom.SLDPRT
138.0 x 6.00 x 38.0 mm
