cruzryan/OpenDOG/CAD/MPU6050 v2.step

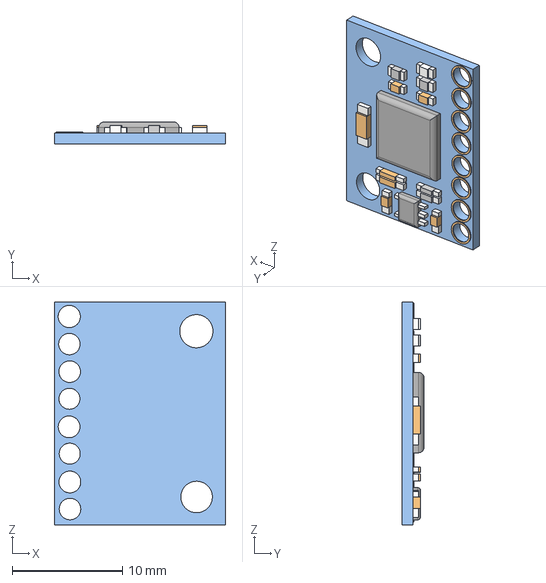
[picture p75: CAD file, 2025-02-11]
CAD/MPU6050 v2.step
15.6 x 2.00 x 20.3 mm
