cruzryan/OpenDOG/CAD/Bones.SLDPRT

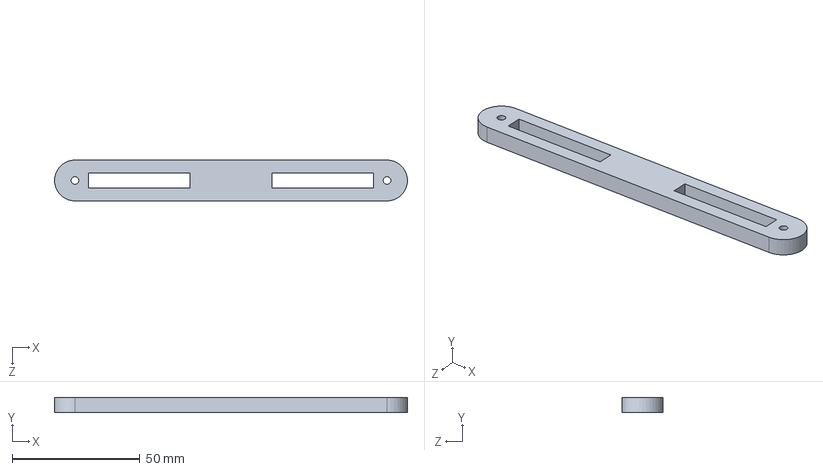
[picture p76: CAD file, 2025-02-11]
CAD/Bones.SLDPRT
138.0 x 6.00 x 16.0 mm
