cruzryan/OpenDOG/Code/quadpilot/body.py

import threading
import time
import socket
import json
import atexit

class QuadPilotBody:
    def __init__(self, ip1="192.168.137.100", ip2="192.168.137.101", listen_for_broadcasts=False):
        self.ips = [ip1, ip2]
        self.UDP_COMMAND_PORT = 12345
        self.UDP_LISTEN_PORT = 12345

        self.sock = socket.socket(socket.AF_INET, socket.SOCK_DGRAM)
        self.sock.setsockopt(socket.SOL_SOCKET, socket.SO_BROADCAST, 1)
        self.sock.settimeout(0.1)

        self._is_closed = False
        self.sock_lock = threading.Lock()

        self.listen_for_broadcasts_flag = listen_for_broadcasts
        self._listener_thread = None
        self._stop_listener_event = threading.Event()

        self.data_access_lock = threading.Lock()
        # Initialize _dmp_data_store for the new DMP data
        self._dmp_data_store = {
            ip: {
                'quaternion': {'w': 0.0, 'x': 0.0, 'y': 0.0, 'z': 0.0},
                'world_accel_mps2': {'ax': 0.0, 'ay': 0.0, 'az': 0.0},
                'ypr_deg': {'yaw': 0.0, 'pitch': 0.0, 'roll': 0.0}
            } for ip in self.ips
        }
        self._motor_data_store = {
            ip: {
                'angles': [0.0]*4, 'encoderPos': [0]*4, 'targetPos': [0]*4,
                'debug': [0]*4, 'debugComputed': [0]*4,
                'dmp_ready': False, # Changed from mpu_available to dmp_ready
                'esp_control_fully_enabled': False,
                'last_packet_received_timestamp_esp': 0.0
            } for ip in self.ips
        }
        self._data_reception_status = {ip: False for ip in self.ips}

        if self.listen_for_broadcasts_flag:
            try:
                self.sock.setsockopt(socket.SOL_SOCKET, socket.SO_REUSEADDR, 1)
                self.sock.bind(('0.0.0.0', self.UDP_LISTEN_PORT))
                self._listener_thread = threading.Thread(target=self._data_listener_loop, daemon=True)
                self._listener_thread.start()
            except Exception as e:
                self.close(); raise e

        atexit.register(self.close)

    def _get_ip_for_motor(self, motor_idx: int):
        if not 0 <= motor_idx <= 7: raise ValueError("Motor index must be 0-7")
        return self.ips[0] if motor_idx < 4 else self.ips[1]

    def _adjust_motor_index_for_esp(self, motor_idx: int):
        return motor_idx % 4

    def _send_command_and_wait_for_ok(self, ip: str, command_data: dict, retries: int = 3, timeout_per_retry: float = 0.5):
        if self._is_closed: return False
        attempt = 0
        message = json.dumps(command_data).encode('utf-8')
        while attempt < retries:
            with self.sock_lock:
                if self._is_closed: return False
                try:
                    self.sock.sendto(message, (ip, self.UDP_COMMAND_PORT))
                    start_time = time.time()
                    while time.time() - start_time < timeout_per_retry:
                        if self._is_closed: return False
                        try:
                            data, addr = self.sock.recvfrom(2048) # Increased buffer for larger DMP packets
                            if addr[0] == ip:
                                response = json.loads(data.decode('utf-8'))
                                if response.get("status") == "OK": return True
                                # Allow broadcast packets to pass through without breaking the loop
                                elif "angles" in response or "dmp_data" in response or "esp_control_fully_enabled" in response:
                                    pass # It's a broadcast packet, ignore for ACK purposes
                                elif "dmp_status" in response: # This is for get_imu_data command response
                                    pass

                        except socket.timeout: break
                        except json.JSONDecodeError: pass # Or log error
                        except OSError:
                             if self._is_closed: return False; break
                        except Exception: break # Or log error
                except Exception: pass # Or log error
            attempt += 1
            if self._is_closed: return False
            if attempt < retries: time.sleep(0.05)
        return False

    def _data_listener_loop(self):
        while not self._stop_listener_event.is_set():
            if self._is_closed: break
            try:
                data, addr = self.sock.recvfrom(2048) # Increased buffer size for potentially larger JSON
                ip_address = addr[0]
                if ip_address not in self.ips:
                    continue  # Ignore packets from unknown IPs

                received_timestamp = time.time()
                json_data = json.loads(data.decode('utf-8'))

                with self.data_access_lock:
                    self._data_reception_status[ip_address] = True
                    current_esp_data_store = self._motor_data_store.get(ip_address)
                    current_dmp_store = self._dmp_data_store.get(ip_address)

                    if not current_esp_data_store or not current_dmp_store:
                        continue # Should not happen if initialized correctly

                    current_esp_data_store['last_packet_received_timestamp_esp'] = received_timestamp

                    # Check for standard motor and status data (always expected in broadcast)
                    if "angles" in json_data and "encoderPos" in json_data:
                        if (len(json_data["angles"]) == 4 and len(json_data["encoderPos"]) == 4):
                            current_esp_data_store['angles'] = json_data["angles"]
                            current_esp_data_store['encoderPos'] = json_data["encoderPos"]
                            current_esp_data_store['targetPos'] = json_data.get("targetPos", current_esp_data_store['targetPos'])
                            # debug fields might not be present anymore if you removed them from ESP
                            current_esp_data_store['debug'] = json_data.get("debug", current_esp_data_store.get('debug', [0]*4))
                            current_esp_data_store['debugComputed'] = json_data.get("debugComputed", current_esp_data_store.get('debugComputed', [0]*4))

                    current_esp_data_store['esp_control_fully_enabled'] = json_data.get("esp_control_fully_enabled", False)

                    # --- MODIFIED PART for DMP data ---
                    is_dmp_ready = json_data.get("dmp_ready", False)
                    current_esp_data_store['dmp_ready'] = is_dmp_ready

                    if is_dmp_ready and "dmp_data" in json_data:
                        dmp_payload = json_data["dmp_data"]
                        if "quaternion" in dmp_payload:
                            current_dmp_store['quaternion'] = dmp_payload["quaternion"]
                        if "world_accel_mps2" in dmp_payload:
                            current_dmp_store['world_accel_mps2'] = dmp_payload["world_accel_mps2"]
                        if "ypr_deg" in dmp_payload:
                            current_dmp_store['ypr_deg'] = dmp_payload["ypr_deg"]
                    elif not is_dmp_ready:
                        # Reset DMP data if DMP is not ready
                        current_dmp_store['quaternion'] = {'w': 0.0, 'x': 0.0, 'y': 0.0, 'z': 0.0}
                        current_dmp_store['world_accel_mps2'] = {'ax': 0.0, 'ay': 0.0, 'az': 0.0}
                        current_dmp_store['ypr_deg'] = {'yaw': 0.0, 'pitch': 0.0, 'roll': 0.0}
                    # --- END OF MODIFIED PART ---

                    # Handling specific "get_imu_data" command responses (which are not broadcasts)
                    # This part might be less relevant if "get_imu_data" command is not used
                    # and all IMU data comes via broadcast.
                    elif "dmp_status" in json_data: # This is a response to get_imu_data
                        if json_data["dmp_status"] == "ready" and "dmp_data" in json_data:
                            dmp_payload = json_data["dmp_data"]
                            current_esp_data_store['dmp_ready'] = True
                            if "quaternion" in dmp_payload:
                                current_dmp_store['quaternion'] = dmp_payload["quaternion"]
                            if "world_accel" in dmp_payload: # ESP code sends world_accel_mps2
                                current_dmp_store['world_accel_mps2'] = dmp_payload["world_accel"]
                            elif "world_accel_mps2" in dmp_payload:
                                current_dmp_store['world_accel_mps2'] = dmp_payload["world_accel_mps2"]
                            if "ypr_deg" in dmp_payload:
                                current_dmp_store['ypr_deg'] = dmp_payload["ypr_deg"]
                        else: # dmp_status is not_ready or error
                            current_esp_data_store['dmp_ready'] = False
                            current_dmp_store['quaternion'] = {'w': 0.0, 'x': 0.0, 'y': 0.0, 'z': 0.0}
                            current_dmp_store['world_accel_mps2'] = {'ax': 0.0, 'ay': 0.0, 'az': 0.0}
                            current_dmp_store['ypr_deg'] = {'yaw': 0.0, 'pitch': 0.0, 'roll': 0.0}

                    # Handle old "imu" key for backward compatibility if necessary,
                    # but prefer "dmp_data"
                    elif "imu" in json_data and "dmp_data" not in json_data:
                        # This is a fallback for the old Adafruit IMU data format
                        # You might want to phase this out or adapt it.
                        # For now, let's assume if "imu" is present, it's raw data and dmp is not ready
                        current_esp_data_store['dmp_ready'] = False
                        # Store it somewhere if needed, or ignore if only DMP data is relevant
                        # self._legacy_imu_data_store[ip_address] = json_data["imu"]


            except socket.timeout:
                continue
            except json.JSONDecodeError:
                # print(f"JSON Decode Error from {ip_address}: {data}") # Optional: for debugging
                pass
            except OSError as e:
                if self._is_closed or self._stop_listener_event.is_set():
                    break
                # print(f"OS Error in listener: {e}") # Optional: for debugging
            except Exception as e:
                if self._is_closed or self._stop_listener_event.is_set():
                    break
                # print(f"General Error in listener: {e}") # Optional: for debugging
                time.sleep(0.01) # Brief pause before retrying

    # --- Getter Methods ---
    def get_latest_motor_data_for_esp(self, ip_index: int):
        if not (0 <= ip_index < len(self.ips)): return None
        ip = self.ips[ip_index]
        with self.data_access_lock:
            return self._motor_data_store.get(ip, {}).copy() if self._data_reception_status.get(ip) else None

    # MODIFIED: Getter for new DMP data
    def get_latest_dmp_data_for_esp(self, ip_index: int):
        if not (0 <= ip_index < len(self.ips)): return {}
        ip = self.ips[ip_index]
        with self.data_access_lock:
            # Return a copy of the dmp data if reception is okay, otherwise an empty dict or default
            if self._data_reception_status.get(ip):
                return self._dmp_data_store.get(ip, {}).copy()
            else:
                return { # Return default structure if no data yet
                    'quaternion': {'w': 0.0, 'x': 0.0, 'y': 0.0, 'z': 0.0},
                    'world_accel_mps2': {'ax': 0.0, 'ay': 0.0, 'az': 0.0},
                    'ypr_deg': {'yaw': 0.0, 'pitch': 0.0, 'roll': 0.0}
                }

    # MODIFIED: to reflect dmp_ready status
    def is_dmp_ready_for_esp(self, ip_index: int):
        if not (0 <= ip_index < len(self.ips)): return False
        ip = self.ips[ip_index]
        with self.data_access_lock:
            return self._motor_data_store.get(ip, {}).get('dmp_ready', False)

    # Kept original IMU getter for backward compatibility if the old "imu" key is still sent by "get_imu_data"
    # but prefer get_latest_dmp_data_for_esp for the new DMP structure.
    def get_latest_imu_data_for_esp(self, ip_index: int):
        """
        DEPRECATED in favor of get_latest_dmp_data_for_esp.
        This might return data if the ESP sends an old "imu" key format in response to get_imu_data.
        """
        if not (0 <= ip_index < len(self.ips)): return {}
        ip = self.ips[ip_index]
        with self.data_access_lock:
             # This was your old structure. If the get_imu_data command returns the old format:
            if "imu" in self._motor_data_store.get(ip, {}): # Check if old key exists
                 return self._motor_data_store.get(ip, {}).get("imu", {}).copy()
            # Otherwise, try to return the new DMP data if available from broadcast
            if self._data_reception_status.get(ip) and self._motor_data_store.get(ip, {}).get('dmp_ready', False):
                return self._dmp_data_store.get(ip, {}).copy()
            return {}

    def is_esp_control_reported_on(self, ip_index: int) -> bool:
        if not (0 <= ip_index < len(self.ips)): return False
        ip = self.ips[ip_index]
        with self.data_access_lock:
            return self._motor_data_store.get(ip, {}).get('esp_control_fully_enabled', False)

    def is_data_available_from_esp(self, ip_index: int):
        if not (0 <= ip_index < len(self.ips)): return False
        ip = self.ips[ip_index]
        with self.data_access_lock:
            return self._data_reception_status.get(ip, False)

    def get_last_packet_received_timestamp_for_esp(self, ip_index: int) -> float:
        if not (0 <= ip_index < len(self.ips)): return 0.0
        ip = self.ips[ip_index]
        with self.data_access_lock:
            return self._motor_data_store.get(ip, {}).get('last_packet_received_timestamp_esp', 0.0)

    def _execute_on_both_esps_parallel(self, command_data_esp1: dict, command_data_esp2: dict,
                                       retries: int, timeout_per_retry: float, join_timeout: float) -> bool:
        results = [False, False]
        def _task(esp_idx, command_data_for_esp):
            results[esp_idx] = self._send_command_and_wait_for_ok(self.ips[esp_idx], command_data_for_esp, retries, timeout_per_retry)

        thread1 = threading.Thread(target=_task, args=(0, command_data_esp1))
        thread2 = threading.Thread(target=_task, args=(1, command_data_esp2))
        thread1.start(); thread2.start()
        thread1.join(timeout=join_timeout); thread2.join(timeout=join_timeout)
        return all(results)

    def set_control_params(self, P: float, I: float, D: float, dead_zone: int, pos_thresh: int) -> bool:
        command = {"command": "set_control_params", "P": P, "I": I, "D": D, "dead_zone": dead_zone, "pos_thresh": pos_thresh}
        return self._execute_on_both_esps_parallel(command.copy(), command.copy(),
                                                   retries=5, timeout_per_retry=1.0, join_timeout=5.5)

    def set_angles(self, angles: list[float]) -> bool:
        if len(angles) != 8: raise ValueError("Exactly 8 angles must be provided")
        angles_int = [int(round(a)) for a in angles]
        cmd1_data = {"command": "set_angles", "angles": angles_int[:4]}
        cmd2_data = {"command": "set_angles", "angles": angles_int[4:]}
        return self._execute_on_both_esps_parallel(cmd1_data, cmd2_data,
                                                   retries=1, timeout_per_retry=0.1, join_timeout=0.3)

    def set_all_pins(self, pins_config: list[tuple[int, int, int, int]]) -> bool:
        if len(pins_config) != 8: raise ValueError("Exactly 8 pin configs must be provided")
        cmd1 = {"command": "set_all_pins"}; cmd2 = {"command": "set_all_pins"}
        for i, p in enumerate(pins_config[:4]):
            cmd1[f"ENCODER_A{i}"]=p[0]; cmd1[f"ENCODER_B{i}"]=p[1]; cmd1[f"IN1_{i}"]=p[2]; cmd1[f"IN2_{i}"]=p[3]
        for i, p in enumerate(pins_config[4:]):
            cmd2[f"ENCODER_A{i}"]=p[0]; cmd2[f"ENCODER_B{i}"]=p[1]; cmd2[f"IN1_{i}"]=p[2]; cmd2[f"IN2_{i}"]=p[3]
        return self._execute_on_both_esps_parallel(cmd1, cmd2,
                                                   retries=5, timeout_per_retry=1.0, join_timeout=5.5)

    def set_control_status(self, motor_idx: int, status: bool) -> bool:
        ip = self._get_ip_for_motor(motor_idx); esp_motor_idx = self._adjust_motor_index_for_esp(motor_idx)
        command = {"command": "set_control_status", "motor": esp_motor_idx, "status": 1 if status else 0}
        return self._send_command_and_wait_for_ok(ip, command, retries=3, timeout_per_retry=0.5)

    def set_all_control_status(self, status: bool) -> bool:
        results = [False, False]
        status_val = 1 if status else 0

        def _task_set_all_motors_on_esp(esp_idx):
            ip_addr = self.ips[esp_idx]
            esp_success = True
            for esp_local_motor_idx in range(4):
                command = {"command": "set_control_status", "motor": esp_local_motor_idx, "status": status_val}
                if not self._send_command_and_wait_for_ok(ip_addr, command.copy(), retries=3, timeout_per_retry=0.5):
                    esp_success = False
                    break
                time.sleep(0.02)
            results[esp_idx] = esp_success

        thread1 = threading.Thread(target=_task_set_all_motors_on_esp, args=(0,))
        thread2 = threading.Thread(target=_task_set_all_motors_on_esp, args=(1,))
        thread1.start(); thread2.start()
        join_timeout_val = 4 * ( (3 * 0.5) + 0.05 ) + 1.0
        thread1.join(timeout=join_timeout_val)
        thread2.join(timeout=join_timeout_val)
        return all(results)

    def reset_all(self) -> bool:
        command = {"command": "reset_all"}
        return self._execute_on_both_esps_parallel(command.copy(), command.copy(),
                                                   retries=5, timeout_per_retry=1.0, join_timeout=5.5)

    def set_send_interval(self, interval_ms: int) -> bool:
        if interval_ms <= 0: interval_ms = 1
        command = {"command": "set_send_interval", "interval": interval_ms}
        return self._execute_on_both_esps_parallel(command.copy(), command.copy(),
                                                   retries=3, timeout_per_retry=0.5, join_timeout=2.0)

    def close(self):
        if not self._is_closed:
            self._is_closed = True; self._stop_listener_event.set()
            if self._listener_thread and self._listener_thread.is_alive(): self._listener_thread.join(timeout=1.0)
            with self.sock_lock:
                try: self.sock.close()
                except Exception: pass
            try: atexit.unregister(self.close)
            except Exception: pass
    def __del__(self): self.close()
